joskwanten/msx-picoverse/2040/software/multirom/wireless/src/ESP8266_memio.asm

; ESP8266 TCP/IP UNAPI BIOS v.1.3
; Oduvaldo Pavan Junior
; ducasp@gmail.com
;    This code implements TCP/IP UNAPI Specification for MSX-SM
;
; Pieces of this code were based on DENYOTCP.ASM (Denyonet ROM)
; made by Konamiman
;
; This code also has contributions from KdL, most specifically in the Wi-Fi
; setup menus and functionality, he has helped quite a lot to get it to the
; final format and functionality, thanks!
;
; The MSX PICO version of this code has contribution from Jeroen Taverne That
; helped making some MACROs on the fixed / non speed optimized loop I/O parts
; of the code so we can easily switch this from I/O based to Memory Based.
;
; Note: this implementation depends upon ESP8266 having the UNAPI
; firmware flashed. This firmware has been developed by me as well.
;
; Usage is free as long as you publish your code changes. If you make a profit
; selling something using this code, a suggestion is that you donate one or two
; pieces of the hardware to the MSX DEV contest to be awarded to MSX DEV winners
; as this shouldn't cost much and perhaps will bring interest on developers to
; make games that support internet :)
;
; Design details:
; There are five instances of this ROM
;
; 1 - If configured as disabled in set-up menu item 4, or through setting F2
;     device to EF or keeping DEL pressed during boot, it won't load at all.
; 2 - F1 is pressed during boot, or through setting F2 device to F1, it will
;     show a setup menu, ESC resume boot.
; 3 - F2 is pressed during a soft reset, or trhough setting F2 device to F2 it
;     will force re-set of the ESP and re-connection to the AP.
; 4 - No key is pressed during a warm boot and F2 device is set to F0, UNAPI 
;     is enabled (default), EXTBIO HOOK for UNAPI calls is installed and HTIM_I
;     hook for internal usage and a few bytes at top of TPA are reserved upon
;     the first UNAPI function being called. No ESP reset or tries to set-up the
;     the RTC are done, so it is a quick warm-boot.
; 5 - No key is pressed during a cold boot or F2 is set to FE or any unknown
;     value, UNAPI is enabled (default), EXTBIO HOOK for UNAPI calls is installed
;     and HTIM_I hook for internal usage and a few bytes at top of TPA are reserved
;     upon the first UNAPI function being called. ESP is reset and if BIOS is set
;     up to do so, SNTP connection attempt is made and RTC is updated
;
; As a ROM, our segment is read only, so for RAM needs we need to use RAM not
; in our page. This ROM will do the following:
;
; If running the SETUP menu, we are going to "borrow" BASIC program area, that
; is saved at TXTTAB. We can't allocate memory at this point as any possible
; disk rom might be sitting on a slot that has not been initialized and results
; could be bad. The BASIC program area trick should be safe, unless some other
; cartridge runs a BASIC software for something (i.e.: wait disks be initialized
; ), in such case, that BASIC software or trick will most likely be corrupted
; after running our setup.
;
; After boot, we need RAM in the 4th page. We have the SLOT WORK AREA for free,
; it is 8 bytes reserved for our slot, and that is certainly not enough, just
; the EXTBIOS HOOK backup cost us 5 bytes, so we have three bytes remaining. Of
; those, we use two to indicate the bottom of the memory reserved in the 4th
; page. Whenever more memory is needed, HIMEM_RESERVED_SIZE must change, just
; remember that more memory reserved means less memory available to
; applications and BASIC, so use it wisely.
;
; Slot Work Area Details
; 0000 - 0004   : EXTBIO hook backup
; 0005 - 0006   : HIMEM Allocated area (starts with 00 xx, once allocated goes
;                 to Fxxx or Exxx so checking 0005 if 00 is enough)
; 007           : Unused
;
; Current HIMEM mapping offset related to the address stored in the 6th and 7th
; bytes of our slot work area:
;
; 0000 - 0004   : HTIM_I hook backup
; 0005 - 0006   : Counter that our HTIM_I hook updates
; 0007          : Store Single Byte some functions need
; 0008          : Stores whether DNS is ready or not
; 0009 - 000A   : Stores last DNS result
; 000B - 000C   : Stores a 16 bits value
; 000D - 0012   : Store a backup of BC / DE / HL
;   000D - 000E : C and B
;   000F - 0010 : D and E
;   0011 - 0012 : H and L
; 0013 - 001D   : Unused
;
; As this is sitting on a slot, there is a resoanable chance that this is initialized
; before any disk controllers. If that is the case, allocating memory at HIMEM is bad
; and might have two bad behaviors:
;
; 1 - Disk Controller is smart enough to determine HIMEM was moved and simply do not
; initialize. No disk available...
; 2 - Disk Controller doesn't care and simply wipe-out memory below original HIMEM at
; boot to create the disk interfaces static work area, thus, causing our allocated
; memory to be overwritten and MSX will most likely crash on ther first VDP interrupt
; after that...
;
; So, allocating memory at cartridge startup will make MSX freeze or misbehave or not
; have the disk available if our ROM is sitting in a slot lower than the disk. There
; are a few possibilities:
;
; 1 - Hook to H_STKE, it is called once all slots have been initialized... But, using
; this hook will make ESE SCSI to not work and halt with a "No enough memory" message,
; so I do not consider it a good option as the intention is to re-use code for other
; adapters.
; 2 - On any UNAPI call check the slot work area if the allocated area is other than 00
; and if it is, execute, otherwise, first execute our allocation routine. This has an
; overhead of a dozen instructions at every UNAPI function we execute, does not seem to
; impact performance compared to the UNAPI RAM driver that doesn't has it
; 3 - Try to go crazy and check for dos roms on slots above us, initialize those first
; if found... Too much trouble for a dozen instructions.
;
; So, for the moment the design decision is option #2
;
; F2 Device by KdL
; That device, present on recent OCM implementations, allow a byte to be saved and
; read from IO address F2. It has FF on start-up, and KdL devised the following
; values/states:
;
; FF - Default, meaning cold boot
; FE - Set this when an unexpected error occurred
; F2 - Equivalent to keeping F2 pressed at boot time, force the next warm boot
;      to try to detect the ESP8266
; F1 - Will force the Wi-Fi setup at next warm boot, so it is not needed to
;      keep F1 pressed
; F0 - Means that RTC has date and time, so the next warm boot doesn't check
;      for F1/F2 or try to update RTC, being faster
; EF - Set when ESP8266 was not found or by user at runtime to disable UNAPI
;      next warm boot
;
; MSX Pico also implements the F2 device

;*************************
;***  BUILD DEFINITIONS **
;*************************

;--- verbose rom...?
NON_VERBOSE_ROM:        equ 0
;--- Use memory mapped IO or not...
USE_MEM_IO:             equ 0

;*******************
;***  CONSTANTS  ***
;*******************

;--- System variables and routines:
CHGMOD:                 equ #005F
CHSNS:                  equ #009C
CHGET:                  equ #009F
CHPUT:                  equ #00A2
BEEP:                   equ #00C0
SNSMAT:                 equ #0141
KILBUF:                 equ #0156
LINLEN:                 equ #F3B0
CLIKSW:                 equ #F3DB
REG2SAV:                equ #F3E1
REG4SAV:                equ #F3E3
TXTTAB:                 equ #F676
ARG:                    equ #F847
HOKVLD:                 equ #FB20
HIMEM:                  equ #FC4A
CSRSW:                  equ #FCA9
EXPTBL:                 equ #FCC1
SLTWRK:                 equ #FD09
H_TIMI:                 equ #FD9F
H_CLEA:                 equ #FED0
EXTBIO:                 equ #FFCA


;--- Memory ports:
MEM_OUT_CMD_PORT:       equ #7F06
MEM_OUT_TX_PORT:        equ #7F07
MEM_IN_DATA_PORT:       equ #7F06
MEM_IN_STS_PORT:        equ #7F07
MEM_PORT_F2:            equ #7F05

;--- I/O ports:
OUT_CMD_PORT:           equ #06
OUT_TX_PORT:            equ #07
IN_DATA_PORT:           equ #06
IN_STS_PORT:            equ #07
PORT_F2:                equ #F2


    if USE_MEM_IO = 1
  MACRO SET_SPEED
    xor a
    ld  (MEM_OUT_CMD_PORT),a            ; Clear UART
  ENDM

  MACRO CLEAR_UART
    ld  a,20
    ld  (MEM_OUT_CMD_PORT),a            ; Clear UART
  ENDM

  MACRO SEND_DATA
    ld  (MEM_OUT_TX_PORT),a             ; Just send, no need to wait response
  ENDM

  MACRO RECEIVE_DATA
    ld a,(MEM_IN_DATA_PORT)
  ENDM

  MACRO LOAD_STS_PORT_IN_A
    ld  a,(MEM_IN_STS_PORT)
  ENDM

  MACRO CHECK_DATA
    ld  a,(MEM_IN_STS_PORT)
    bit 0,a                         ; If nz has data
  ENDM

  MACRO CHECK_QUICK_RECEIVE
    ld  a,(MEM_IN_STS_PORT)
    bit 3,a                         ; Quick Receive Supported?
  ENDM

  MACRO CHECK_BUFFER_UNDERRUN
    ld  a,(MEM_IN_STS_PORT)
    bit 4,a                         ; Buffer underrun?
  ENDM

  MACRO READ_F2
    ld  a,(MEM_PORT_F2)
  ENDM

  MACRO WRITE_F2
    ld  (MEM_PORT_F2),a
  ENDM
    else

  MACRO SET_SPEED
    xor a
    out (OUT_CMD_PORT),a            ; Clear UART
  ENDM

  MACRO CLEAR_UART
    ld  a,20
    out (OUT_CMD_PORT),a            ; Clear UART
  ENDM

  MACRO SEND_DATA
    out (OUT_TX_PORT),a             ; Just send, no need to wait response
  ENDM

  MACRO RECEIVE_DATA
    in a,(IN_DATA_PORT)
  ENDM

  MACRO LOAD_STS_PORT_IN_A
    in  a,(IN_STS_PORT)
  ENDM

  MACRO CHECK_DATA
    in  a,(IN_STS_PORT)
    bit 0,a                         ; If nz has data
  ENDM

  MACRO CHECK_QUICK_RECEIVE
    ld  a,(IN_STS_PORT)
    bit 3,a                         ; Quick Receive Supported?
  ENDM

  MACRO CHECK_BUFFER_UNDERRUN
    in  a,(IN_STS_PORT)
    bit 4,a                         ; Buffer underrun?
  ENDM

  MACRO READ_F2
    in  a,(PORT_F2)
  ENDM

  MACRO WRITE_F2
    out (PORT_F2),a
  ENDM
    endif

;--- API version and implementation version:
API_V_P:                equ 1
API_V_S:                equ 2
ROM_V_P:                equ 1
ROM_V_S:                equ 3

;--- Size of memory to reserve in upper TPA:
HIMEM_RESERVED_SIZE     equ 30

;--- Layout of our TPA area:
H_TIM_BACKUP_OFFSET     equ 0
MEMORY_COUNTER_OFFSET   equ 5
MEMORY_SB_VAR_OFFSET    equ 7
MEMORY_DNS_READY_OFFSET equ 8
MEMORY_DNS_RES_OFFSET   equ 9
MEMORY_DB_VAR_OFFSET    equ #0B
MEMORY_REGBACKUP_OFFSET equ #0D
MEMORY_BCBACKUP_OFFSET  equ #0D
MEMORY_DEBACKUP_OFFSET  equ #0F
MEMORY_HLBACKUP_OFFSET  equ #11

;--- Scan Page Size
SCAN_MAX_PAGE_SIZE      equ 8

;--- Maximum number of available standard and implementation-specific function
;--- numbers. Must be 0 to 127.
MAX_FN:                 equ 29

;--- Must be either zero (if no implementation-specific functions available),
;--- or 128 to 254.
MAX_IMPFN:              equ 0

;--- TCP/IP UNAPI error codes:
ERR_OK:                 equ 0
ERR_NOT_IMP:            equ 1
ERR_NO_NETWORK:         equ 2
ERR_NO_DATA:            equ 3
ERR_INV_PARAM:          equ 4
ERR_QUERY_EXISTS:       equ 5
ERR_INV_IP:             equ 6
ERR_NO_DNS:             equ 7
ERR_DNS:                equ 8
ERR_NO_FREE_CONN:       equ 9
ERR_CONN_EXISTS:        equ 10
ERR_NO_CONN:            equ 11
ERR_CONN_STATE:         equ 12
ERR_BUFFER:             equ 13
ERR_LARGE_DGRAM:        equ 14
ERR_INV_OPER:           equ 15

;--- TCP/IP UNAPI connection Status
UNAPI_TCPIP_NS_CLOSED   equ 0
UNAPI_TCPIP_NS_OPENING  equ 1
UNAPI_TCPIP_NS_OPEN     equ 2
UNAPI_TCPIP_NS_UNKNOWN  equ 255

;************************
;***  MSX ROM HEADER  ***
;************************
    org #4000
    db                  #41,#42
    dw                  INIT        ; Initialize ESP, if not found, won't install hook
    dw                  0           ; Statement
    dw                  0           ; Device
    dw                  0           ; Text
    ds                  6           ; Reserved

;==================
;===  Start-up  ===
;==================

INIT:
    ld  a,h                         ; Let's test if we are mirrored and being executed in wrong page
    cp  #40                         ; is MSB 0x40?
    ret nz                          ; if not, return, it is a mirror
    ; Let's set some System Variables
    xor a                           ; a = #00
    ld  (CSRSW),a                   ; cursor display is disabled
    ld  (CLIKSW),a                  ; when key press, key click disabled
    ; Let's intercept [DEL] key
    ld  a,8
    call    SNSMAT
    bit 3,a                         ; Test [DEL]
    ret z                           ; If DEL is pressed, UNAPI driver is not loaded and exits
    ; Let's check the Screen Mode, ref. https://www.msx.org/wiki/VDP_Table_Base_Address_Registers
    ld  a,(REG2SAV)
    cp  2
    jp  z,SCREEN_SETUP              ; If yes, is SCREEN 3
    ld  a,(REG4SAV)
    cp  0
    jr  z,IS_SCREEN1                ; If yes, is SCREEN 1
SCREEN_SETUP:
    ; Let's set the SCREEN 1
    ld  a,1                         ; a = #01
    rst #30
    db  0
    dw  CHGMOD                      ; SCREEN 1
IS_SCREEN1:
    ld  a,29                        ; WIDTH 29
    ld  (LINLEN),a
    ; We check if the Port F2 device is available
    READ_F2                         ; a = #FF, default value if it comes from power off or hard reset
    cpl                             ; a = #FF - a
    ld  c,a                         ; c = #00
    WRITE_F2                        ; a = #00
    ; Wait 250ms to ensure a successful hard reset even if you press the button very quickly
    call    WAIT_250MS_AND_THEN_CONTINUE
    READ_F2                         ; a = #00?
    cpl                             ; a = #FF - a
    WRITE_F2                        ; a = #FF?
    push    af
    ld  a,#FE                       ; Preset #FE, unexpected error
    WRITE_F2                        ; on port #F2
    pop af
    cp  c                           ; If not a = c, port #F2 is writable and available
    jr  z,BOOT_FROM_POWER_OFF       ; If a = c, port #F2 is not available, let's proceed as "boot from power off"
    ; Ok, Port F2 device available
    cp  #EF                         ; UNAPI driver has been disabled
    jr  nz,NOT_DISABLED_BY_F2       ; No, let's continue checking
    WRITE_F2                        ; If yes, UNAPI driver is not loaded and exits, but need to restore F2 port to not have a false error
    ret                             ; And our work is done
NOT_DISABLED_BY_F2:
    cp  #F0                         ; UNAPI driver has been loaded at least once
    jp  nz, F2_IS_NOT_F0            ; Ok, has not been loaded
    ; Let's intercept [F1] key
    ld  a,6
    call    SNSMAT
    bit 5,a                         ; Test [F1]
    jp  z,ENTERING_ESPSETUP         ; If F1 is pressed, let's execute our setup menu
    ; F1 is not pressed, continue
    bit 6,a                         ; Test [F2]
    jp  nz,INIT_UNAPI               ; If F2 is not pressed, let's proceed to INIT_UNAPI
    ; F2 is not pressed, continue
    jp  INIT_NOCLOCKUPDAT2          ; If yes, proceed without affecting the connection or the date and time
F2_IS_NOT_F0:
    cp  #F1                         ; User requested to go directly to Wi-Fi Setup
    jp  z,ENTERING_ESPSETUP         ; If yes, let's execute our setup menu
    cp  #F2                         ; User forces to check if ESP is installed
    jp  z,F2_IS_PRESSED             ; If yes, let's go check it out
    cp  #FE                         ; Unexpected error from the previous reboot
    jr  nz,BOOT_FROM_POWER_OFF      ; If no one is confirmed, let's proceed as "boot from power off"
    ; Oops! An unexpected error occurred on the last reboot
    ld  hl,STR_OOPS                 ; Print Oops! An unexpected error message
    call    PRINTHL                 ; and let's proceed as "boot from power off"
    ld  b,120                       ; Wait 2 seconds with message on screen
WAIT_2S:
    halt
    djnz    WAIT_2S                 ; If not zero, our time out has not elapsed
    ld  a,CLS
    call    CHPUT
BOOT_FROM_POWER_OFF:
    ; Let's intercept [F1] key
    ld  a,6
    call    SNSMAT
    bit 5,a                         ; Test [F1]
    jp  z,ENTERING_ESPSETUP         ; If F1 is pressed, let's execute our setup menu
    ; F1 is not pressed, continue
    if  NON_VERBOSE_ROM = 0
    ld  hl,WELCOME
    call    PRINTHL
    CHECK_QUICK_RECEIVE
    jr  nz,BOOT_FROM_POWER_OFF.1    ; QR Supported
    ld  hl,WELCOME_SF2
    call    PRINTHL
    jr  BOOT_FROM_POWER_OFF.2
BOOT_FROM_POWER_OFF.1:
    ld  hl,WELCOME_SF
    call    PRINTHL
BOOT_FROM_POWER_OFF.2:
    endif
    ld  a,6
    call    SNSMAT
    bit 6,a                         ; Test [F2]
    jp  nz,INIT_UNAPI               ; If F2 is not pressed, let's proceed to INIT_UNAPI
    ; F2 is pressed, continue
F2_IS_PRESSED:
    call    RESET_ESP
    or  a
    jr  nz,ESP_NOT_FOUND
    ld  hl,OK_S                     ; Properly detected
    jp  INIT_F_MSG                  ; Well, if reset successful, continue
ESP_NOT_FOUND:
    ; If here, ESP was not found, so, exit with an error message
    ld  a,b
    or  a
    ld  hl,FAIL_S                   ; If 0, non responsive
    jr  z,INIT_F_MSG
    ld  hl,FAIL_F                   ; Otherwise, firmware is old
INIT_F_MSG:
    call    PRINTHL
INIT_F_WAIT:
    ld  b,180                       ; 3s
INIT_F_LOOP_WAIT:
    halt
    djnz    INIT_F_LOOP_WAIT
AND_DONE:
    ld  a,#EF                       ; Set #EF, ESP Not Found
    WRITE_F2                        ; on port #F2
    ret                             ; And done
INIT_UNAPI:
    CLEAR_UART
    ld  a,CMD_QUERY_ACLK_SETTINGS
    SEND_DATA
    ld  hl,60                       ; Wait Up To 1s
    ld  de,(TXTTAB)                 ; We will borrow Basic Program memory area for now...
    ld  ixl,e
    ld  ixh,d                       ; Address in IX
    call    WAIT_MENU_CMD_RESPONSE
    jp  z,INIT_NOCLOCKUPDATE        ; If error, just skip
    ; Response received, IX+0 and IX+1 has Auto Clock and GMT
    ld  a,3
    cp  (ix+0)
    jr  nz,INIT_UNAPI2              ; If not disabled continue on INIT_UNAPI2
    ; Disabled, ok, so let's ensure connection is not locked (just in case it was setup as disabled right now)
    CLEAR_UART
    ld  a,CMD_WIFIRELEASE_ESP
    SEND_DATA                       ; Just send, no need to wait response
    ret
INIT_UNAPI2:
    ld  a,(#002D)                   ; Check MSX Version
    or  a
    jr  z,INIT_NOCLOCKUPDATE        ; If zero, MSX1, can't set clock
    xor a
    or  (ix+0)
    jr  z,INIT_NOCLOCKUPDATE        ; if turned off, skip
    ; Ok, not zero, so we are going to simply request the time, it might take up to 10s
    inc ix
    inc ix                          ; ok, leave IX+0 and IX+1 intact
    ; b = number of response check attempts
    ld  b,5                         ; 5 * 2s = 10s
    CLEAR_UART
    ld  a,CMD_GET_TIME
    SEND_DATA
TRY_AGAIN:
    push    bc
    ld  hl,120                      ; Wait Up To 2s per attempt
    call    WAIT_MENU_CMD_RESPONSE
    jr  nz,INIT_CLOCKUPDATE         ; if ok, follow up
    ld  hl,STR_WAITING              ; Print Waiting for connection message
    call    PRINTHL
    ld  a,#ff
    cp  b                           ; Was time-out the failure reason?
    pop bc                          ; Restore stack ballance and retry counter
    jr  nz,STOP_TRYING              ; If error return code and not time-out, no more checks needed
    ld  a,CMD_GET_TIME              ; Needed for retries
    djnz    TRY_AGAIN
STOP_TRYING:
    ; Leave a message that clock has not been updated
    ld  hl,STR_CLKUPDT_FAIL
    call    PRINTHL
    ld  a,240                       ; Wait 4 seconds with message on screen
WAIT_4S:
    halt
    dec a
    ; If not zero, our time out has not elapsed
    jr  nz,WAIT_4S
    jr  INIT_NOCLOCKUPDATE          ; error, just skip to not set garbage in clock
INIT_CLOCKUPDATE:
    pop bc
    dec ix
    dec ix                          ; ix back where it should
    ; ix + 0 -> 0 If no need to set clock, 1 if set clock, 2 if set clock and request to turn Wi-Fi Off
    ; ix + 1 -> GMT setting, well, not going to use it
    ; ix + 2 -> Seconds
    ; ix + 3 -> Minutes
    ; ix + 4 -> Hours
    ; ix + 5 -> Day
    ; ix + 6 -> Month
    ; ix + 7 -> Year LSB
    ; ix + 8 -> Year MSB
    ld  h,(ix+4)
    ld  l,(ix+3)
    ld  d,(ix+2)
    call    SET_TIME
    jr  nz,INIT_NOCLOCKUPDATE       ; if error, just skip
    ld  h,(ix+8)
    ld  l,(ix+7)
    ld  d,(ix+6)
    ld  e,(ix+5)
    call    SET_DATE
    ld  a,2
    cp  (ix+0)
    jr  nz,INIT_NOCLOCKUPDATE
    ; First, release any hold to Wi-Fi Connection
    CLEAR_UART
    ld  a,CMD_WIFIRELEASE_ESP
    SEND_DATA                       ; Just send, no need to wait response
    ; And, turn off Wi-Fi Immediatelly
    CLEAR_UART
    ld  a,CMD_WIFI_OFF
    SEND_DATA                       ; Just send, no need to wait response
    jr  INIT_NOCLOCKUPDAT2
INIT_NOCLOCKUPDATE:
    ; Release any hold to Wi-Fi Connection
    CLEAR_UART
    ld  a,CMD_WIFIRELEASE_ESP
    SEND_DATA                       ; Just send, no need to wait response
INIT_NOCLOCKUPDAT2:
    ; Save existing EXTBIO hook if it exists
    ld  a,(HOKVLD)
    bit 0,a
    jr  nz,SAVE_HOOK2               ; HOKVLD tells us if there is an extended BIOS already or not, if yes, save it
    ; If here, no extended BIOS
    call    GETSLT
    call    GETWRK                  ; Our ROM work area address is at HL (we can use up to 8 bytes)
    ld  a,#c9                       ; RET, as we are the first extended BIOS
    ld  (hl),a
    jr  PATCH                       ; And now all we need to do is patch the EXTBIO hook :)

SAVE_HOOK2:
    ; If here, we are not the first to extend bios, so we need to save the previous one
    call    GETSLT
    call    GETWRK                  ; Our ROM work area address is at HL (we can use up to 8 bytes)
    ex  de,hl                       ; It is the destination for....
    ld  hl,EXTBIO                   ; The actual EXTBIO hook
    ld  bc,5                        ; That is 5 bytes large
    ldir                            ; And move to our work area
    xor a
    ld  (de),a                      ; Not initialized (de is at the sixth byte) of our slot work area
    inc de
    ld  (de),a                      ; Not initialized (de is at the seventh byte) of our slot work area

    ; Patch EXTBIO
PATCH:
    ld  a,#F7                       ; RST #30
    ld  (EXTBIO),a                  ; In EXTBIO hook
    call    GETSLT                  ; Our Slot in A
    ld  (EXTBIO+1),a                ; Next EXTBIO hook byte
    ld  hl,DO_EXTBIO                ; Our EXTBIO routine address
    ld  (EXTBIO+2),hl               ; Goes to the following two bytes in the hook

    ld  hl,EXTBIO+5                 ; Must patch DISINT and ENAINT as well
    ld  b,5*2
PATCH2:
    ld  (hl),#C9
    inc hl
    djnz    PATCH2                  ; So patch all 10 bytes with return

    ld  hl,HOKVLD
    set 0,(hl)                      ; And set HOKVLD properly to indicate an EXTBIOS is installed
INIT_OK:
    if  NON_VERBOSE_ROM = 0
    ld  hl,OK_S                     ; All done and set, nice exit message
    call    PRINTHL
    endif
    ld  a,#F0                       ; Set #F0, UNAPI driver has been loaded at least once
    WRITE_F2
    ret

;==============================
;===  TPA Memory Allocation  ==
;==============================
HIMEM_ALLOC:
    ; Now let's reserve memory in the 4th page for our usage
    ld hl,(HIMEM)                   ; Get HIMEM
    or  a                           ; Clear Carry
    ld  de,HIMEM_RESERVED_SIZE      ; Reserve How much memory we need
    sbc hl,de                       ; New HIMEM
    ld  (HIMEM),hl                  ; Save it
    inc hl                          ; To be safe
    ex  de,hl                       ; now in DE
    call    GETSLT
    call    GETMEMPOINTERADDR       ; This is where we are going to store our memory area address
    ; GETSLT and GETMEMPOINTER do not change DE, so it still has the our memory area address
    ld  (hl),e
    inc hl
    ld  (hl),d                      ; And save our memory area there
    ; Ok, DE has our memory area, let's save old H_TIMI hook there
    ld  hl,H_TIMI                   ; The actual H_TIMI hook
    ld  bc,5                        ; That is 5 bytes large
    ldir                            ; And move to our memory area
    di                              ; Turn of interrupts as we are going to patch H_TIMI
PATCH_H_TIMI:
    ld  a,#F7                       ; RST #30
    ld  (H_TIMI),a                  ; In H_TIMI hook
    call    GETSLT                  ; Our Slot in A
    ld  (H_TIMI+1),a                ; Next H_TIMI hook byte
    ld  hl,DO_HTIMI                 ; Our H_TIMI routine address
    ld  (H_TIMI+2),hl               ; Goes to the following two bytes in the hook
    ei                              ; done, so re-enable interrupts

    ; Set DNS_READY to zero
    xor a
    call    SETDNSREADY
    ; Set TIME-OUT counter to zero
    ld  hl,0
    call    SETCOUNTER
    ret

;============================
;===  SETUP Menu Routines  ==
;===       Main Menu       ==
;============================
ESPSETUP.EXIT:
    ld  a,CLS
    call    CHPUT
    jp  INIT_UNAPI                  ; When done, resume initialization
ENTERING_ESPSETUP:
    ld  hl,ENTERING_WIFI_SETUP
    call    PRINTHL
    call    PATTERN_SETUP
    call    WAIT_250MS_AND_THEN_CONTINUE
    ; Hold Wi-Fi Connection On
    CLEAR_UART
    ld  a,CMD_WIFIHOLD_ESP
    SEND_DATA
    ld  hl,60                       ; Up to 1s time-out
    call    WAIT_MENU_CMD_RESPONSE  ; Wait response
    ; We do not want to error here, just in case user still need to upgrade ESP firmware
ESPSETUP:
    call    RESET_ESP
    or  a
    jp  nz,ESP_NOT_FOUND            ; Not well, ESP was not found
    ; Well, if reset successful, continue
    ld  hl,WELCOME
    call    PRINTHL
    CHECK_QUICK_RECEIVE
    jr  nz,ESPSETUP.2NF             ; If yes, tells Quick Receive support
    ld  hl,WELCOME_SF2
    call    PRINTHL                 ; Print Welcome message no QR
    jr  ESPSETUP.3NF
ESPSETUP.2NF:
    ld  hl,WELCOME_SF
    call    PRINTHL                 ; Print Welcome message QR
ESPSETUP.3NF:
    ld  hl,WELCOME_CS
    call    PRINTHL                 ; Print Wi-Fi is reconnecting to:
ESPSETUP_NEXT:
    call    KILBUF                  ; Clear Keyboard Buffer
    ld  hl,WELCOME_NEXT
    call    PRINTHL
    ld  hl,WELCOME_SF_NEXT
    call    PRINTHL                 ; Print Empty Welcome message
    call    GET_AP_STAT
    jp  z,ESPSETUP_NEXT.1G          ; Won't block in case of error
    ; Success, so connection state is in IX+0, then, zero terminated string with SSID starting at IX+1
    ld  a,(ix+0)
    ld  hl,WELCOME_CS0_NEXT
    cp  0
    jr  z,ESPSETUP_NEXT.2F
    ld  hl,WELCOME_CS1_NEXT
    cp  1
    jr  z,ESPSETUP_NEXT.2F
    ld  hl,WELCOME_CS2_NEXT
    cp  2
    jr  z,ESPSETUP_NEXT.2F
    ld  hl,WELCOME_CS3_NEXT
    cp  3
    jr  z,ESPSETUP_NEXT.2F
    ld  hl,WELCOME_CS4_NEXT
    cp  4
    jr  z,ESPSETUP_NEXT.2F
    ld  hl,WELCOME_CS5_NEXT
ESPSETUP_NEXT.2F:
    ld  iyh,a                       ; Save current conn status in iyh
    call    PRINTHL                 ; Print Status
    push    ix
    pop hl
    inc hl                          ; HL has AP Name
    call    PRINTHLINE              ; Print AP Name
ESPSETUP_NEXT.1G:
    ld  hl,MMENU_S_NEXT
    call    PRINTHL                 ; Print Main Menu
MM_CURSOR_BLINK:
    call    MM_CURSOR_SW            ; Cursor On
CONN_CHG_LOOP:
    call    CHSNS
    jr  nz,MM_WAIT_INPUT            ; If not zero, there is a key in buffer
    ; Ok, there is not, we can check if connection status changed
    call    GET_AP_STAT
    jp  z,CONN_CHG_LOOP             ; Won't block in case of error
    ; Success, so connection state is in IX+0
    ld  a,(ix+0)
    cp  iyh                         ; If same, zero
    jr  z,CONN_CHG_LOOP             ; Keep loop
    call    MM_CURSOR_SW            ; Cursor Off
    jp  ESPSETUP_NEXT               ; Changed, re-build menu
MM_WAIT_INPUT:
    call    CHGET
    cp  #1b                         ; ESC?
    jp  z,ESPSETUP.EXIT             ; When done, resume initialization
    cp  '1'                         ; Setup Nagle?
    jp  z,SET_NAGLE
    cp  '2'                         ; Setup Wi-Fi On Period?
    jp  z,SET_WIFI_TIMEOUT
    cp  '3'                         ; Scan networks?
    jp  z,START_WIFI_SCAN
    cp  '4'                         ; Automatic Setting of Clock?
    jp  z,START_CLK_AUTO
    call    BEEP                    ; Wrong Input, beep
    call    MM_CURSOR_SW            ; Cursor Off
    halt
    jp  MM_CURSOR_BLINK             ; And return, waiting another key
MM_CURSOR_SW:                       ; Cursor workaround for CONN_CHG_LOOP
    ld  a,GOLEFT
    call    CHPUT
    ld  a,1
    ld  (CSRSW),a
    ld  a,' '
    call    CHPUT                   ; Switch the cursor display mode
    xor a
    ld  (CSRSW),a
    ret
GET_AP_STAT:                        ; Use 'call GET_AP_STAT'
    CLEAR_UART
    ld  a,CMD_AP_STS
    SEND_DATA                       ; Get AP conn status and name
    ld  hl,60                       ; Wait Up To 1s
    ld  de,(TXTTAB)                 ; We will borrow Basic Program memory area for now...
    ld  ixl,e
    ld  ixh,d                       ; Address in IX
    jp  WAIT_MENU_CMD_RESPONSE

;============================
;===  SETUP Menu Routines  ==
;===  Wi-Fi and Clock Menu ==
;============================
CLK_MSX1_GO:
    ld  hl,MMENU_CLOCK_MSX1
    call    PRINTHL                 ; Print Main Clock MSX1 message
    call    ISCLKAUTO
    ld  a,(ix+0)                    ; Auto Clock Current setting
    cp  3                           ; If 3 adapter disabled
    jr  z,CLK_MSX1_ADAPTERDIS
    ld  hl,MMENU_CLOCK_0
    call    PRINTHL
    jr  CLK_MSX1_OPT
CLK_MSX1_ADAPTERDIS:
    ld  hl,MMENU_CLOCK_3
    call    PRINTHL
CLK_MSX1_OPT:
    ld  hl,MMENU_CLOCK_OPT
    call    PRINTHL
CLK_MSX1_WAIT_OPT_INPUT:
    call    CHGET
    cp  #1b                         ; ESC?
    jp  z,ESPSETUP                  ; Back to main menu
    cp  '0'
    jp  z,CLK_MSX1_SEND_CMD
    cp  '3'
    jp  z,CLK_AUTO_WAIT_GMT
    call    BEEP                    ; Wrong Input, beep
    jp  CLK_MSX1_WAIT_OPT_INPUT     ; And return, waiting another key
CLK_MSX1_SEND_CMD:
    call    CHPUT                   ; Print option
    sub '0'                         ; Adjust format
    ld  (ix+0),a                    ; Save it
    ld  a,#0d
    call    CHPUT
    ld  a,#0a
    call    CHPUT
    jp  CLK_AUTO_GMT_CHK_DONE       ; And sending the command will be done there

START_CLK_AUTO:
    ld  a,'4'
    call    CHPUT
    call    WAIT_250MS_AND_THEN_CONTINUE
    ld  a,(#002D)                   ; Check MSX Version
    or  a
    jp  z,CLK_MSX1_GO               ; If zero, MSX1, so can just enable or disable adapter
CLK_AUTO_GO:
    ld  hl,MMENU_CLOCK_MSX2
    call    PRINTHL                 ; Print Main Clock MSX2 message
    call    ISCLKAUTO
    ld  a,(ix+0)                    ; Auto Clock Current setting
    or  a                           ; If zero, off
    jr  nz,CLK_AUTO_CHK1
    ld  hl,MMENU_CLOCK_0
    call    PRINTHL
    jr  CLK_AUTO_GMT_OPT
CLK_AUTO_CHK1:
    dec a                           ; If 1, on and keep wifi on
    jr  nz,CLK_AUTO_CHK2
    ld  hl,MMENU_CLOCK_1
    call    PRINTHL
    jr  CLK_AUTO_GMT
CLK_AUTO_CHK2:
    dec a                           ; If 2, on and turn wifi off
    jr  nz,CLK_AUTO_3
    ld  hl,MMENU_CLOCK_2
    call    PRINTHL
    jr  CLK_AUTO_GMT
CLK_AUTO_3:
    ld  hl,MMENU_CLOCK_3
    call    PRINTHL
    jr  CLK_AUTO_GMT_OPT
CLK_AUTO_GMT:
    ld  h,(ix+1)                    ; Save it for now
    ld  a,(ix+1)                    ; GMT current setting
    bit 7,a                         ; If set, is -
    jr  z,CLK_AUTO_GMTP
    ld  a,'-'
    call    CHPUT
    res 7,(ix+1)                    ; Clear - indicator
    jr  CLK_AUTO_GMTM
CLK_AUTO_GMTP:
    ld  a,'+'
    call    CHPUT
CLK_AUTO_GMTM:
    ld  a,9
    cp  (ix+1)                      ; Greater than 9?
    jr  nc,CLK_AUTO_GMTD            ; If not, just print what is in A + '0'
    ld  a,'1'                       ; It is 1
    call    CHPUT
    ld  a,(ix+1)
    add '0'-10                      ; Need to subtract 10 and add '0' to print
    call    CHPUT
    jr  CLK_AUTO_GMT_OPT
CLK_AUTO_GMTD:
    ld  a,'0'
    add a,(ix+1)                    ; Our value
    call    CHPUT
    ld  (ix+1),h                    ; Restore original value
CLK_AUTO_GMT_OPT:
    ld  hl,MMENU_CLOCK_OPT
    call    PRINTHL
CLK_AUTO_WAIT_OPT_INPUT:
    call    CHGET
    cp  #1b                         ; ESC?
    jp  z,ESPSETUP                  ; Back to main menu
    cp  '0'
    jp  z,CLK_AUTO_WAIT_GMT
    cp  '1'
    jp  z,CLK_AUTO_WAIT_GMT
    cp  '2'
    jp  z,CLK_AUTO_WAIT_GMT
    cp  '3'
    jp  z,CLK_AUTO_WAIT_GMT
    call    BEEP                    ; Wrong Input, beep
    jp  CLK_AUTO_WAIT_OPT_INPUT     ; And return, waiting another key
CLK_AUTO_WAIT_GMT:
    call    CHPUT                   ; Print option
    sub '0'                         ; Adjust format
    ld  (ix+0),a                    ; Save it
    or  a
    jp  z,CLK_AUTO_GMT_CHK_DONE     ; And send the command if just disabling clock auto set
    cp  3
    jp  z,CLK_AUTO_GMT_CHK_DONE     ; Or send the command if just disabling the adapter
    ld  hl,MMENU_GMT_OPT
    call    PRINTHL
    ld  d,0                         ; # of digits entered
    ld  e,0                         ; # of characters printed
    ld  (ix+1),0                    ; GMT 0
CLK_AUTO_WAIT_GMT_INPUT:
    call    CHGET
    cp  #1b                         ; ESC?
    jp  z,ESPSETUP                  ; Back to main menu
    cp  #0d                         ; ENTER?
    jp  z,CLK_AUTO_GMT_CHK_INPUT    ; Check if ok to send command
    cp  #08                         ; Backspace?
    jp  z,CLK_AUTO_GMT_CHK_BS       ; Check if there is something to erase
    cp  '-'                         ; Negative value?
    jp  z,CLK_AUTO_GMT_CHK_INPUT
    cp  '0'                         ; >=0?
    jp  c,CLK_AUTO_GMT_BAD_INPUT    ; If not, bad input
    cp  '9'+1                       ; <= 9
    jp  nc,CLK_AUTO_GMT_BAD_INPUT   ; If not, bad input
    jp  CLK_AUTO_GMT_CHK_INPUT      ; Otherwise, validate digit
CLK_AUTO_GMT_CHK_BS:
    xor a
    cp  e                           ; Anything on screen?
    jr  z,CLK_AUTO_GMT_BAD_INPUT    ; Nothing to erase
    dec e                           ; One less character on the screen
    cp  d                           ; Any digit?
    jr  z,CLK_AUTO_GMT_CHK_BS_MIN   ; If not, just erase - sign
    ; There is, so it is one less digit
    dec d
    jr  CLK_AUTO_GMT_CHK_DIGIT
CLK_AUTO_GMT_CHK_BS_MIN:
    ld  (ix+1),0                    ; Reset sign
CLK_AUTO_GMT_CHK_DIGIT:
    ld  a,8                         ; Backspace
    call    CHPUT                   ; Print it
    ld  a,' '                       ; Space
    call    CHPUT                   ; Print it
    ld  a,8                         ; Backspace
    call    CHPUT                   ; Print it
    jp  CLK_AUTO_WAIT_GMT_INPUT     ; Return
CLK_AUTO_GMT_BAD_INPUT:
    ; Beep might use sub rom, and if so, all registers will be messed up, better save
    push    bc
    push    de
    push    af
    push    hl
    call    BEEP                    ; Wrong Input, beep
    pop hl
    pop af
    pop de
    pop bc
    jp  CLK_AUTO_WAIT_GMT_INPUT     ; And return, waiting another key
CLK_AUTO_GMT_CHK_INPUT:
    ld  c,a                         ; Save in C for printing if needed
    cp  '-'                         ; - sign?
    jr  nz,CLK_AUTO_GMT_CHK_CR      ; If not, check if enter
    ; - sign
    ld  a,0
    cp  e                           ; If not the first character, can't accept
    jr  nz,CLK_AUTO_GMT_BAD_INPUT
    ; It is the first, so let's print it
    ld  a,c
    call    CHPUT
    ld  (ix+1),0x80                 ; Set the - sign bit, for now rest is zero
    inc e                           ; Increase # of characters printed
    jp  CLK_AUTO_WAIT_GMT_INPUT     ; Continue waiting input
CLK_AUTO_GMT_CHK_CR:
    cp  #0d                         ; ENTER?
    jr  nz,CLK_AUTO_GMT_CHK_CD      ; If not, check if digit is valid
    ; Enter
    ld  a,0
    cp  d                           ; Ok, at least one digit entered?
    jr  z,CLK_AUTO_GMT_BAD_INPUT    ; No, so, enter is no good now
    ; It is, if it had a digit entered and did not send, it was 1, so...
    ld  a,1
    or  a,(ix+1)                    ; Adjust sign, if needed
    ld  (ix+1),a                    ; Save
    jr  CLK_AUTO_GMT_CHK_DONE       ; Ok, ready to send
CLK_AUTO_GMT_CHK_CD:
    ; Ok, it is a digit
    ld  b,'0'
    sub a,b                         ; A has digit value
    ld  b,a                         ; Save in B
    ld  a,0
    cp  d
    jr  nz,CLK_AUTO_GMT_CHK_CSD     ; If not zero, it is second digit, so almost done
    ; 1st digit, let's check if it is other than 1, if it is, we are almost done
    ld  a,1
    cp  b
    jr  z,CLK_AUTO_GMT_CHK_CD.1     ; If it is 1, wait next digit or enter
    ; Not 1, so just adjust ix+1 and go
    ld  a,c
    call    CHPUT                   ; Print it
    ld  a,b
    or  a
    jr  z,CLK_AUTO_SKIP_SIGN
    or  a,(ix+1)                    ; Adjust sign, if needed
CLK_AUTO_SKIP_SIGN:
    ld  (ix+1),a                    ; Save
    jr  CLK_AUTO_GMT_CHK_DONE       ; Ok, ready to send
CLK_AUTO_GMT_CHK_CD.1:
    ld  a,c
    call    CHPUT                   ; Print it
    inc d                           ; Digits entered now is 1
    inc e                           ; Digits printed increased
    jp  CLK_AUTO_WAIT_GMT_INPUT     ; Continue waiting input
CLK_AUTO_GMT_CHK_CSD:
    ; Second digit, easy... First was 1, now need to check if it is 0, 1 or 2, otherwise, bad entry
    ld  a,b
    ld  b,3
    cp  b
    jp  nc,CLK_AUTO_GMT_BAD_INPUT   ; 3 or more, so, not valid
    or  a                           ; Is it zero?
    jr  nz,CLK_AUTO_GMT_CHK_CSD1    ; If not, check for 1
    ; It was zero
    ld  a,10                        ; So, 10
    or  a,(ix+1)                    ; Adjust sign, if needed
    ld  (ix+1),a                    ; Save
    ld  a,c
    call    CHPUT                   ; Print it
    jr  CLK_AUTO_GMT_CHK_DONE       ; Ready to
CLK_AUTO_GMT_CHK_CSD1:
    dec a                           ; Is it one?
    jr  nz,CLK_AUTO_GMT_CHK_CSD2
    ; It was one
    ld  a,11                        ; So, eleven
    or  a,(ix+1)                    ; Adjust sign, if needed
    ld  (ix+1),a                    ; Save
    ld  a,c
    call    CHPUT                   ; Print it
    jr  CLK_AUTO_GMT_CHK_DONE       ; Ready to send
CLK_AUTO_GMT_CHK_CSD2:
    ; It was two
    ld  a,12                        ; So, twelve
    or  a,(ix+1)                    ; Adjust sign, if needed
    ld  (ix+1),a                    ; Save
    ld  a,c
    call    CHPUT                   ; Print it
    ; And send command
CLK_AUTO_GMT_CHK_DONE:
    ld  a,#0d
    call    CHPUT
    ld  a,#0a
    call    CHPUT
    ld  hl,STR_SENDING
    call    PRINTHL
    CLEAR_UART
    ld  a,CMD_SET_ACLK_SETTINGS
    SEND_DATA
    ld  a,0                         ; Size MSB is 0
    SEND_DATA
    ld  a,2                         ; Size LSB is 2
    SEND_DATA
    ld  a,(ix+0)                    ; Option
    SEND_DATA
    ld  a,(ix+1)                    ; GMT
    SEND_DATA
    ld  hl,60                       ; Wait Up To 1s
    ld  a,CMD_SET_ACLK_SETTINGS
    call    WAIT_MENU_QCMD_RESPONSE
    ld  hl,STR_SENDING_OK
    jr  nz,CLK_AUTO_GMT_CHK_RESULT
    ld  hl,STR_SENDING_FAIL
CLK_AUTO_GMT_CHK_RESULT:
    call    PRINTHL
    jp  WAIT_2S_AND_THEN_MAINMENU

;============================
;===  SETUP Menu Routines  ==
;===    Wi-Fi Scan Menu    ==
;============================
START_WIFI_SCAN:
    ld  a,'3'
    call    CHPUT
    call    WAIT_250MS_AND_THEN_CONTINUE
START_WIFI_RESCAN:
    ld  hl,MMENU_SCAN
    call    PRINTHL                 ; Print Main Scan message
    call    STARTWIFISCAN           ; Request Wi-Fi Scan to start
    ld  de,(TXTTAB)                 ; We will borrow Basic Program memory area for now...
    ld  ixl,e
    ld  ixh,d                       ; Address in IX
    ld  de,20                       ; At least 10s waiting scan to finish, retry 20 times waiting 0.5s between attempts
WIFI_SCAN_WAIT_END:
    CLEAR_UART
    ld  a,CMD_SCAN_RESULTS
    SEND_DATA
    ld  hl,60                       ; Wait Up To 1s
    call    WAIT_MENU_SCMD_RESPONSE
    jp  nz,WIFI_SCAN_SHOW_LIST      ; if success show the list
    ld  a,b
    cp  2                           ; If 2, scan is done and nothing found
    jp  z,WIFI_SCAN_NONETWORKS
    ld  l,30
WIFI_SCAN_WAITHS:
    halt
    dec l
    jr  nz,WIFI_SCAN_WAITHS
    dec de
    ld  a,e
    or  d
    jp  z,WIFI_SCAN_TIMEOUT
    jp  WIFI_SCAN_WAIT_END
WIFI_SCAN_SHOW_LIST:
    ld  d,a                         ; Save access point counter here
    ld  e,0                         ; And here how many were printed
    ld  hl,MMENU_SCANS
    call    PRINTHL
    push    ix
    pop hl                          ; IX in HL
WIFI_LIST_LOOP:
    ld  a,e
    add a,'0'                       ; Convert to number
    call    CHPUT
    ld  a,' '                       ; Space
    call    CHPUT
    ld  a,'-'                       ; Dash
    call    CHPUT
    ld  a,' '                       ; Space
    call    CHPUT
    ld  b,24                        ; Cuts AP names > 23 chars
PRT_APNAMELP:
    ld  a,(hl)
    or  a
    jp  z,PRT_APENC
    call    CHPUT
    inc hl
    djnz    PRT_APNAMELP
    push    hl
    ld  hl,SCAN_TERMINATOR_CUT
    call    PRINTHL
    pop hl
PRT_APNAMELP_CUT:
    ld  a,(hl)
    or  a
    jp  z,PRT_APENC
    inc hl
    jp  PRT_APNAMELP_CUT
PRT_APENC:
    inc hl
    ld  a,(hl)
    or  a
    jp  z,PRT_APNOTENC
    push    hl
    ld  hl,SCAN_TERMINATOR_ENC
    call    PRINTHL
    pop hl
    jp  PRT_AP_CHKLOOP
PRT_APNOTENC:
    push    hl
    ld  hl,SCAN_TERMINATOR_OPEN
    call    PRINTHL
    pop hl
PRT_AP_CHKLOOP:
    inc hl
    inc e
    ld  a,SCAN_MAX_PAGE_SIZE
    cp  e
    jp  z,APLIST_OVERFLOW
    dec d
    jp  nz,WIFI_LIST_LOOP
    ld  b,0                         ; Signal no more list data
    jr  APLIST_NO_OVERFLOW
APLIST_OVERFLOW:
    dec d                           ; Update remaining items
    xor a
    or  d                           ; Still has items?
    jr  z,APLIST_NO_OVERFLOW        ; No more items
    ld  b,1                         ; Signal that there still is data pending to list in another page
    push    hl
    pop iy                          ; Save in IY the address to continue from
    ld  c,d                         ; And C has the remaining AP count
    ld  hl,MMENU_SCANQM
    jr  APLIST_NOFLW
APLIST_NO_OVERFLOW:
    ; If here, current page has been printed
    ; E has the maximum allowable AP number
    ; B will indicate if there are more items for a next page
    ; IY will hold the address of the following items
    ; Let's ask which one to connect
    ld  hl,MMENU_SCANQ
APLIST_NOFLW:
    call    PRINTHL                 ; Show message asking which network to connect
    ld  a,'0'
    add a,e
    ld  e,a                         ; To make it easy in the selection screen
WIFI_SELECT_AP:
    call    CHGET
    cp  #1b                         ; ESC?
    jp  z,ESPSETUP                  ; When done, back to main setup
    cp  #20                         ; Spacebar?
    jp  z,WIFI_SELECT_SPACEBAR      ; Check if re-scan or next page
    cp  CR                          ; ENTER?
    jp  z,WIFI_CONNECT_ME_CHOOSEN   ; Request AP Name and Password if needed
    cp  '0'                         ; Check if A is less than 0
    jp  c,INPUT_WFSAP_BAD_INPUT     ; If it is, ignore
    cp  e                           ; Check if a is greater than what is in E
    jp  nc,INPUT_WFSAP_BAD_INPUT    ; If it is, ignore
    jp  WIFI_CONNECT_SELECTION_OK   ; Selection Ok if here

WIFI_SELECT_SPACEBAR:
    xor a
    or  d                           ; D = AP counter
    jp  z,START_WIFI_RESCAN         ; Rescan if no more items
    ; Otherwise, more items, start at IY
    push    iy
    pop ix                          ; Restore the list from where we finished last time
    ld  a,c                         ; Restore the remaining APs to list
    jp  WIFI_SCAN_SHOW_LIST         ; And show

WIFI_CONNECT_ME_CHOOSEN:
    ld  hl,MMENU_MANUALENTRY
    call    PRINTHL                 ; Show message asking AP details....
    ; IX has the AP list, we don't care, but that address is ours to use to handle SSID Entry
    push    ix
    pop hl                          ; HL has the address
    ld  c,0                         ; AP name size
WIFI_CONNECT_MANUAL_ENTRY:
    call    CHGET
    cp  #1b                         ; ESC?
    jp  z,ESPSETUP                  ; Back to main setup
    cp  #08                         ; Backspace?
    jr  z,WIFI_CONNECT_ME_BS        ; Check if there is something to erase
    cp  #0d                         ; ENTER?
    jr  z,WIFI_ME_CHECK_INPUT       ; Check if ok
    ; Otherwise it is a digit
    ld  (hl),a
    ld  a,c
    sub 32                          ; SSID maximum is 32 characters
    jr  z,WIFI_CONNECT_MANUAL_ENTRY
    ld  a,(hl)
    inc c
    inc hl
    cp  32
    jr  nc,WIFI_CONNECT_ME_CHKPRT2  ; Ok, not below space, but is it delete?
    ld  a,'?'                       ; Prints a question mark
    jr  WIFI_CONNECT_ME_CHKPRTD
WIFI_CONNECT_ME_CHKPRT2:
    cp  #7f
    jr  nz,WIFI_CONNECT_ME_CHKPRTD
    ld  a,'?'                       ; Prints a question mark if it is delete
WIFI_CONNECT_ME_CHKPRTD:
    call    CHPUT                   ; Print a char
    jp  WIFI_CONNECT_MANUAL_ENTRY
WIFI_CONNECT_ME_0_TERM:
    xor a
    ld  (hl),a
    inc hl
    push    hl                      ; Save it
    ld  hl,MENU_MANUALENTRY_PWD
    call    PRINTHL                 ; We are asking if password is needed
    pop hl                          ; Restore it
    call    CHGET                   ; Get key, if Y or y, needed, otherwise not
    res 5,a                         ; Force upper case
    cp  'Y'
    jr  z,WIFI_CONNECT_ME_PWD_Y     ; And tell using encryption
    ld  a,'n'
    call    CHPUT                   ; Overwrite what was typed with 'n'
    xor a                           ; Ok, if here, no pwd, so no encryption
    jr  WIFI_CONNECT_ME_PWD
WIFI_CONNECT_ME_PWD_Y:
    ld  a,'y'
    call    CHPUT                   ; Print 'y'
    ld  a,1                         ; Do not change flags, pwd needed
WIFI_CONNECT_ME_PWD:
    ld  (hl),a                      ; Save if encryption is expected
    push    ix
    pop hl                          ; HL containing the beginning of SSID name
    ld  a,#0d
    call    CHPUT
    ld  a,#0a
    call    CHPUT
    jp  WIFI_CONNECT_AP_PWDQ        ; And the rest is handled like if menu selected
WIFI_CONNECT_ME_BS:
    xor a
    cp  c                           ; Has any data to delete?
    jr  z,WIFI_CONNECT_MANUAL_ENTRY ; No
    ; Yes
    dec hl                          ; Decrement pointer
    dec c                           ; Decrement counter
    ld  a,8                         ; Backspace
    call    CHPUT                   ; Print it
    ld  a,' '                       ; Space
    call    CHPUT                   ; Print it
    ld  a,8                         ; Backspace
    call    CHPUT                   ; Print it
    jr  WIFI_CONNECT_MANUAL_ENTRY   ; Return
WIFI_ME_CHECK_INPUT:
    xor a
    cp  c                           ; Has received any data?
    jr  z,WIFI_CONNECT_MANUAL_ENTRY ; No
    jp  WIFI_CONNECT_ME_0_TERM      ; Yes, so handle SSID input termination

WIFI_CONNECT_SELECTION_OK:
    call    CHPUT                   ; Valid input, print it
    ld  e,'0'
    sub a,e                         ; Get in decimal
    ld  e,a                         ; Back in E
    ; IX has the AP list, A which one has been selected, now our routine will do it
    ld  a,#0d
    call    CHPUT
    ld  a,#0a
    call    CHPUT
    push    ix
    pop hl                          ; put IX in HL
WIFI_CONNECT_AP_SRCH:
    ld  a,e
    or  a
WIFI_CONNECT_AP_SRCH.1:
    jp  z,WIFI_CONNECT_AP_PWDQ
    ld  a,(hl)
    inc hl
    or  a
    jp  nz,WIFI_CONNECT_AP_SRCH.1   ; Find string terminator
    ; Found, jump encryption byte
    inc hl
    dec e                           ; Decrement selection, if 0 we are done
    jp  nz,WIFI_CONNECT_AP_SRCH.1
WIFI_CONNECT_AP_PWDQ:
    ; HL has the address of AP name string
    ld  d,h
    ld  e,l                         ; Save copy in D
    ld  bc,0                        ; BC will have the ap connection data length
WIFI_CONNECT_APSIZE:
    inc bc
    ld  a,(de)
    inc de
    or  a
    jp  nz,WIFI_CONNECT_APSIZE      ; Count size, including zero terminator
    ; Check for encryption
    ld  a,(de)
    or  a
    jp  z,WIFI_CONNECT_SENDCMD      ; If no password requested, good to go
    ; Shoot, need to request password, well, let's do it
    push    hl                      ; Save HL
    ld  hl,MMENU_ASKPWD
    call    PRINTHL                 ; Inform that user need to input PWD
    pop hl                          ; Restore HL
    ld  iy,0                        ; IY will help in backspacing
    ld  ixh,1                       ; Start hidden
WIFI_CONNECT_RCV_PWD:
    call    CHGET
    cp  #1b                         ; ESC?
    jp  z,ESPSETUP                  ; When done, back to main setup
    cp  #08                         ; Backspace?
    jp  z,WIFI_CONNECT_RCV_PWD_BS   ; Check if there is something to erase
    cp  #0d                         ; ENTER?
    jp  z,WIFI_PWD_CHECK_INPUT      ; Check if ok
    cp  #7f                         ; Delete?
    jp  z,WIFI_CONNECT_RCV_PWDH     ; Change password from clear to hidden or vice versa
WIFI_CONNECT_RCV_PWD_STR:
    ; Ok, so it is a digit and store
    ld  (de),a
    ld  a,iyl
    sub 63                          ; 63 chars password limit (WPA2 encryption)
    jr  z,WIFI_CONNECT_RCV_PWD
    ld  a,(de)
    inc bc
    inc de
    inc iy                          ; Increment counters and pointer
    push    af                      ; Save A
    ld  a,ixh
    or  a                           ; If zero, print char, otherwise print *
    jr  z,WIFI_CONNECT_RCV_PWD_CHAR
    pop af
    ld  a,'*'                       ; Print * and keep password hidden
    call    CHPUT
    jp  WIFI_CONNECT_RCV_PWD        ; And back to receiving digits
WIFI_CONNECT_RCV_PWD_CHAR:
    pop af
    cp  32
    jr  nc,WIFI_CONNECT_RCV_CHKPRT2 ; Ok, not below space, but is it delete?
    ld  a,'?'                       ; Prints a question mark
    jr  WIFI_CONNECT_RCV_CHKPRTD
WIFI_CONNECT_RCV_CHKPRT2:
    cp  #7f
    jr  nz,WIFI_CONNECT_RCV_CHKPRTD
    ld  a,'?'                       ; Prints a question mark if it is delete
WIFI_CONNECT_RCV_CHKPRTD:
    call    CHPUT                   ; Print a char
    jp  WIFI_CONNECT_RCV_PWD        ; And back to receiving digits

WIFI_CONNECT_RCV_PWDH:
    ld  a,iyl
    or  iyh
    jp  nz,WIFI_CONNECT_RCV_PWD_STR ; If digits entered, can't change password behavior, so it is a pass phrase char
    xor a
    or  ixh
    ld  ixh,1
    jr  z,WIFI_CONNECT_RCV_PWD      ; Return if it was 0
    ld  ixh,0
    jr  z,WIFI_CONNECT_RCV_PWD      ; Otherwise set to 0 and return

WIFI_CONNECT_RCV_PWD_BS:
    ld  a,iyl
    or  iyh
    jp  z,WIFI_CONNECT_RCV_PWD      ; If no digits entered, nothing to erase
    dec iy                          ; Decrement counter
    dec bc                          ; Decrement counter
    dec de                          ; Decrement pointer
    ld  a,8                         ; Backspace
    call    CHPUT                   ; Print it
    ld  a,' '                       ; Space
    call    CHPUT                   ; Print it
    ld  a,8                         ; Backspace
    call    CHPUT                   ; Print it
    jp  WIFI_CONNECT_RCV_PWD        ; Return

WIFI_PWD_CHECK_INPUT:
    ld  a,iyl
    or  iyh
    jp  z,WIFI_CONNECT_RCV_PWD      ; If no digits entered, no password to send
    ; Otherwise done and ready to send
WIFI_CONNECT_SENDCMD:
    call    WAIT_250MS_AND_THEN_CONTINUE
    push    hl
    ld  HL,MMENU_CONNECTING
    call    PRINTHL
    pop hl
    ; Print AP name
    push    hl
    call    PRINTHLINE              ; Print AP Name
    pop hl
    ; HL has the address of our data, BC the data size, so it is just needed to send the command
    CLEAR_UART
    ld  a,CMD_WIFI_CONNECT
    SEND_DATA
    ld  a,b                         ; Size MSB is in B
    SEND_DATA
    ld  a,c                         ; Size LSB is in c
    SEND_DATA
WIFI_CONNECT_SENDCMDLP:
    ld  a,(hl)
    SEND_DATA
    inc hl
    dec bc
    ld  a,b
    or  c
    jp  nz,WIFI_CONNECT_SENDCMDLP
    ld  hl,600                      ; Wait Up To 10s
    ld  a,CMD_WIFI_CONNECT          ; Our command
    call    WAIT_MENU_QCMD_RESPONSE
    jp  z,WIFI_CONNECT_FAIL
    ld  hl,STR_SENDING_OK_JN        ; Success
    call    PRINTHL
    jp  WAIT_2S_AND_THEN_MAINMENU
WIFI_CONNECT_FAIL:
    ld  hl,STR_SENDING_NOK_JN       ; Failure
    call    PRINTHL
    jp  WAIT_4S_AND_THEN_MAINMENU

INPUT_WFSAP_BAD_INPUT:
    push    bc
    push    de
    push    af
    push    hl
    push    ix
    push    iy
    call    BEEP                    ; Wrong Input, beep
    pop iy
    pop ix
    pop hl
    pop af
    pop de
    pop bc
    jp WIFI_SELECT_AP               ; Return

WIFI_SCAN_NONETWORKS:
    ld  hl,MMENU_SCANN
    call    PRINTHL
    jp  WAIT_4S_AND_THEN_MAINMENU

WIFI_SCAN_TIMEOUT:
    ld  hl,MMENU_SCANF
    call    PRINTHL
    jp  WAIT_4S_AND_THEN_MAINMENU

SET_WIFI_TIMEOUT:
    ld  a,'2'
    call    CHPUT
    call    WAIT_250MS_AND_THEN_CONTINUE
    ld  hl,MMENU_TIMEOUT
    call    PRINTHL                 ; Print Main Timeout message
    call    CHECKTIMEOUT            ; TimeOut is on or off?
    jp  z,WIFI_SET_ALWAYS_ON        ; If 0, always on
    ; Otherwise there is a timeout
    push    hl
    ld hl,MMENU_TIMEOUT_NOTALWAYSON1
    call    PRINTHL
    pop hl
    call    PRINTHL
    ld hl,MMENU_TIMEOUT_NOTALWAYSON2
    call    PRINTHL
    ld  d,0                         ; Count digits
    jr  INPUT_TIMEOUT
WIFI_SET_ALWAYS_ON:
    ld  hl,MMENU_TIMEOUT_ALWAYSON
    call    PRINTHL
    ld  de,(TXTTAB)                 ; We will borrow Basic Program memory area for now...
    ld  ixl,e
    ld  ixh,d                       ; Address in IX
    ld  d,0                         ; Count digits
INPUT_TIMEOUT:
    call    CHGET
    cp  #1b                         ; ESC?
    jp  z,ESPSETUP                  ; When done, back to main setup
    cp  #0d                         ; ENTER?
    jp  z,SET_WIFI_CHECK_INPUT      ; Check if ok
    cp  #08                         ; Backspace?
    jp  z,SET_WIFI_BS_INPUT         ; Check if there is something to erase
    cp  '0'                         ; Check if A is less than 0
    jp  c,INPUT_TIMEOUT_BAD_INPUT   ; if it is, ignore
    cp  '9'+1                       ; Check if a is greater than  9
    jp  nc,INPUT_TIMEOUT_BAD_INPUT  ; If it is, ignore
    ld  (ix+0),a                    ; Save it
    call    CHPUT                   ; It is valid, so print it
    inc d                           ; Increment digit count
    inc ix                          ; Increment pointer
    ld  a,3
    cp  d
    jp  z,SET_WIFI_CHECK_INPUT      ; All we can do is accept up to 3 digits, check if ok
    jp  INPUT_TIMEOUT               ; Not done yet, so continue

INPUT_TIMEOUT_BAD_INPUT:
    call    BEEP                    ; Wrong Input, beep
    jp INPUT_TIMEOUT                ; Return

SET_WIFI_BS_INPUT:
    xor a
    or  d                           ; Counter has any digit?
    jp  z,INPUT_TIMEOUT             ; Nope, so just continue
    dec d                           ; Decrement counter
    dec ix                          ; Decrement pointer
    ld  a,8                         ; Backspace
    call    CHPUT                   ; Print it
    ld  a,' '                       ; Space
    call    CHPUT                   ; Print it
    ld  a,8                         ; Backspace
    call    CHPUT                   ; Print it
    jp  INPUT_TIMEOUT               ; Return

SET_WIFI_CHECK_INPUT:
    xor a
    or  d                           ; Counter has any digits
    jp  z,INPUT_TIMEOUT             ; Nope, so just continue
    ; IX is pointing one position after last digit, so revert
    dec ix
    ld  a,(ix+0)                    ; Digit in A
    sub '0'                         ; Convert it to decimal
    ld  h,0                         ; First digit, so H is 0
    ld  l,a                         ; And L has the digit
    dec d                           ; If digits finished, just set
    jp  z,SET_WIFI_EXECUTE_SET_COMMAND
    dec ix
    ld  a,(ix+0)                    ; Digit in A
    sub '0'                         ; Convert it to decimal
    add a,a                         ; A*2
    ld  c,a                         ; A*2 in C
    add a,a                         ; A*4
    add a,a                         ; A*8
    add a,c                         ; A*10
    ; Up to here, we can get 90 + 9, 99, won't go to H anyway, just add to L
    add a,l                         ; L has the first digit
    ld  l,a                         ; And now L has the two digits
    dec d                           ; If digits finished, just set
    jp  z,SET_WIFI_EXECUTE_SET_COMMAND
    dec ix
    ld  a,(ix+0)                    ; Digit in A
    sub '0'                         ; Convert it to decimal
    add a,a                         ; A*2
    ld  c,a                         ; A*2 in C
    add a,a                         ; A*4
    add a,a                         ; A*8
    add a,c                         ; A*10
    ex  de,hl                       ; Get the two digits results in de
    ld  l,a
    ld  h,0                         ; HL = A*10
    add hl,hl                       ; HL = A*20
    ld  c,l
    ld  b,h                         ; BC = A*20
    add hl,hl                       ; HL = A*40
    add hl,hl                       ; HL = A*80
    add hl,bc                       ; HL = A*100
    add hl,de                       ; HL = three digits result
    ; This was the last digit, up to three
SET_WIFI_EXECUTE_SET_COMMAND:
    jp  SET_ESP_WIFI_TIMEOUT        ; And set and done

;============================
;===  SETUP Menu Routines  ==
;===      NAGLE Menu       ==
;============================
SET_NAGLE:
    ld  a,'1'
    call    CHPUT
    call    WAIT_250MS_AND_THEN_CONTINUE
    ld  hl,MMENU_NAGLE
    call    PRINTHL                 ; Print Main Nagle message
    call    CHECKNAGLE              ; Nagle is on or off?
    jr  nz,NAGLE_IS_ON              ;
    ld  hl,MMENU_NAGLE_OFF          ; Show the menu telling nagle is off
    call    PRINTHL                 ; Print options
SET_NAGLE_WI_ON:
    call    CHGET
    cp  #1b                         ; ESC?
    jp  z,ESPSETUP                  ; When done, back to main setup
    cp  'O'                         ; Toggle Nagle On
    jp  z,SET_NAGLE_ON              ;
    cp  'o'                         ; Toggle Nagle On
    jp  z,SET_NAGLE_ON              ;
    call    BEEP                    ; Wrong Input, beep
    jp  SET_NAGLE_WI_ON             ; And return waiting key

NAGLE_IS_ON:
    ld  hl,MMENU_NAGLE_ON           ; Show the menu telling nagle is on
    call    PRINTHL                 ; Print options
SET_NAGLE_WI_OFF:
    call    CHGET
    cp  #1b                         ; ESC?
    jp  z,ESPSETUP                  ; When done, back to main setup
    cp  'O'                         ; Toggle Nagle Off
    jp  z,SET_NAGLE_OFF             ;
    cp  'o'                         ; Toggle Nagle Off
    jp  z,SET_NAGLE_OFF             ;
    call    BEEP                    ; Wrong Input, beep
    jp  SET_NAGLE_WI_OFF            ; And return waiting key

;============================
;===  SETUP Menu Routines  ==
;===  Auxiliary Functions  ==
;============================
SET_ESP_WIFI_TIMEOUT:
    ex  de,hl
    ld  a,#0d
    call    CHPUT
    ld  a,#0a
    call    CHPUT
    ld  hl,STR_SENDING              ; Indicate it is sending a command
    call    PRINTHL
    CLEAR_UART
    ld  a,CMD_TIMER_SET
    SEND_DATA
    xor a                           ; Size MSB is 0
    SEND_DATA
    ld  a,2                         ; Size LSB is 2
    SEND_DATA
    ld  a,d                         ; Timeout MSB
    SEND_DATA
    ld  a,e                         ; Timeout LSB
    SEND_DATA
    ld  hl,60                       ; Wait Up To 1s
    ld  a,CMD_TIMER_SET             ; Our command
    call    WAIT_MENU_QCMD_RESPONSE
    jp  z,MENU_BAD_END
    ld  hl,STR_SENDING_OK           ; Success
    call    PRINTHL
    jp  WAIT_2S_AND_THEN_MAINMENU

SET_NAGLE_OFF:
    ld  a,'O'
    call    CHPUT
    ld  a,#0d
    call    CHPUT
    ld  a,#0a
    call    CHPUT
    ld  hl,STR_SENDING              ; Indicate it is sending a command
    call    PRINTHL
    CLEAR_UART
    ld  a,CMD_NAGLE_OFF
    SEND_DATA
    ld  hl,60                       ; Wait Up To 1s
    call    WAIT_MENU_QCMD_RESPONSE
    jp  z,MENU_BAD_END
    ld  hl,STR_SENDING_OK           ; Success
    call    PRINTHL
    jp  WAIT_2S_AND_THEN_MAINMENU

STARTWIFISCAN:
    CLEAR_UART
    ld  a,CMD_SCAN_START
    SEND_DATA
    ld  hl,60                       ; Wait Up To 1s
    call    WAIT_MENU_QCMD_RESPONSE
    ret nz                          ; If success return
    ld  a,CR
    call    CHPUT
    ld  a,LF
    call    CHPUT
    jp  MENU_SUB_BAD_END            ; If error, nothing much to do, main menu

SET_NAGLE_ON:
    ld  a,'O'
    call    CHPUT
    ld  a,#0d
    call    CHPUT
    ld  a,#0a
    call    CHPUT
    ld  hl,STR_SENDING              ; Indicate it is sending a command
    call    PRINTHL
    CLEAR_UART
    ld  a,CMD_NAGLE_ON
    SEND_DATA
    ld  hl,60                       ; Wait Up To 1s
    call    WAIT_MENU_QCMD_RESPONSE
    jp  z,MENU_BAD_END
    ld  hl,STR_SENDING_OK           ; Success
    call    PRINTHL
    jp  WAIT_2S_AND_THEN_MAINMENU

WAIT_4S_AND_THEN_MAINMENU:
    ld  a,240                       ; Wait 4 seconds with message on screen
    jr  WAIT_AND_THEN_MAINMENU
WAIT_2S_AND_THEN_MAINMENU:
    ld  a,120                       ; Wait 2 seconds with message on screen
WAIT_AND_THEN_MAINMENU:
    call    WAIT_BEFORE_CONTINUING
    jp  ESPSETUP                    ; When done, back to main setup
WAIT_250MS_AND_THEN_CONTINUE:
    ld  a,15                        ; Wait 250 ms then continue
WAIT_BEFORE_CONTINUING:
    halt
    dec a
    ; If not zero, our time out has not elapsed
    jr  nz,WAIT_BEFORE_CONTINUING
    ret                             ; Time out and continue

; Check Auto Clock
ISCLKAUTO:
    CLEAR_UART
    ld  a,CMD_QUERY_ACLK_SETTINGS
    SEND_DATA
    ld  hl,60                       ; Wait Up To 1s
    ld  de,(TXTTAB)                 ; We will borrow Basic Program memory area for now...
    ld  ixl,e
    ld  ixh,d                       ; address in IX
    call    WAIT_MENU_CMD_RESPONSE
    jp  z,MENU_SUB_BAD_END
    ; Response received, IX+0 and IX+1 has Auto Clock and GMT, A
    ret

; Check what is the current NAGLE setting
CHECKNAGLE:
    CLEAR_UART
    ld  a,CMD_QUERY_ESP_SETTINGS
    SEND_DATA
    ld  hl,60                       ; Wait Up To 1s
    ld  de,(TXTTAB)                 ; We will borrow Basic Program memory area for now...
    ld  ixl,e
    ld  ixh,d                       ; Address in IX
    call    WAIT_MENU_CMD_RESPONSE
    jp  z,MENU_SUB_BAD_END
    ; Response received, nagle is the first one, ON: or OFF:
    ld  a,'O'
    cp  (ix+0)
    jp  nz,MENU_SUB_BAD_END
    ld  a,'N'
    cp  (ix+1)
    jp  nz,CHECK_NAGLE_OFF
    ld  a,':'
    cp  (ix+2)
    jp  nz,MENU_SUB_BAD_END
    or  a                           ; It will make it NZ
    ret
CHECK_NAGLE_OFF:
    ld  a,'F'
    cp  (ix+1)
    jp  nz,MENU_SUB_BAD_END
    ld  a,'F'
    cp  (ix+2)
    jp  nz,MENU_SUB_BAD_END
    ld  a,':'
    cp  (ix+3)
    jp  nz,MENU_SUB_BAD_END
    ; Already has zero, so just ret
    ret

; Check what is the current TIMEOUT setting, return 0 if always on, otherwise there is a timeout
; Will return a zero terminated string @ HL that can be printed
; Will return the value in DE
CHECKTIMEOUT:
    CLEAR_UART
    ld  a,CMD_QUERY_ESP_SETTINGS
    SEND_DATA
    ld  hl,60                       ; Wait Up To 1s
    ld  de,(TXTTAB)                 ; We will borrow Basic Program memory area for now...
    ld  ixl,e
    ld  ixh,d                       ; Address in IX
    call    WAIT_MENU_CMD_RESPONSE
    jp  z,MENU_SUB_BAD_END
    ; Response received, nagle is the first one, ON: or OFF:
    ld  a,':'
    inc ix
    inc ix                          ; Nagle response is two or three bytes long, let's check
    dec bc
    dec bc                          ; Remaining bytes
    cp  (ix+0)
    jp  z,CHECKTIMEOUT.1
    inc ix
    dec bc                          ; Remaining bytes
    cp  (ix+0)
    jp  nz,MENU_SUB_BAD_END         ; If not here, sorry to say it is an error
CHECKTIMEOUT.1:
    ld  a,b
    or  c                           ; All data read?
    jp  z,MENU_SUB_BAD_END          ; If so, sorry to say it is an error
    inc ix                          ; At the first digit
    dec bc                          ; Remaining bytes
    ld  a,b
    or  c                           ; All data read?
    jp  z,MENU_SUB_BAD_END          ; If so, sorry to say it is an error
    push    ix                      ; This is the start of the string, save it
    ld  h,0                         ; No digit so far
    ; It can have up to three digits
CHECKTIMEOUT.2:
    ld  a,':'
    cp  (ix+0)                      ; Check if it is the separator
    jp  z,CHECKTIMEOUT.3            ; If it is routine will follow through
    ld  a,(ix+0)                    ; Get the supposed digit in A
    ld  l,'9'+1
    cp  l
    jp  nc,MENU_SUB_BAD_END_1S      ; If more than '9', sorry to say it is an error
    ld  l,'0'
    cp  l
    jp  c,MENU_SUB_BAD_END_1S       ; If less than '0', sorry to say it is an error
    inc h                           ; It is not, so it is a digit
    ld  a,3
    cp  h
    jp  c,MENU_SUB_BAD_END_1S       ; If more than three digits, sorry to say it is an error
    inc ix                          ; Increase pointer
    dec bc                          ; Decrease remaining
    ld  a,b
    or  c                           ; All data read?
    jp  nz,CHECKTIMEOUT.2           ; Not, so rinse and repeat
CHECKTIMEOUT.3:
    ld  (ix+0),0                    ; Null terminate string value
    dec ix
    ld  a,(ix+0)                    ; 1st Digit in A
    sub '0'                         ; Convert it to decimal value
    ld  e,a
    ld  d,0                         ; DE has first digit
    dec h                           ; Decrement digit counter
    jr  z,CHECKTIMEOUT.END          ; If all digits, done
    ; Now second digit, multiply it by 10 and add to E, even if 90 + 9, still fits E
    dec ix
    ld  a,(ix+0)                    ; 2nd Digit
    sub '0'                         ; Convert it to decimal value
    add a,a                         ; A has *2
    ld  c,a                         ; C has *2
    add a,a                         ; A has *4
    add a,a                         ; A has *8
    add a,c                         ; A has *10
    add a,e                         ; A has two digits result
    ld  e,a                         ; Back to E, DE has two digits results
    dec h                           ; Decrement digit counter
    jr  z,CHECKTIMEOUT.END          ; If all digits, done
    ; Now Third digit, multiply it by 100 and add to DE
    dec ix
    ld  a,(ix+0)                    ; 3rd Digit
    sub '0'                         ; Convert it to decimal value
    add a,a                         ; A has *2
    ld  c,a                         ; C has *2
    add a,a                         ; A has *4
    add a,a                         ; A has *8
    add a,c                         ; A has *10
    ld  h,0
    ld  l,a                         ; HL has *10
    add hl,hl                       ; HL has *20
    ld  b,h
    ld  c,l                         ; BC has *20
    add hl,hl                       ; HL has *40
    add hl,hl                       ; HL has *80
    add hl,bc                       ; HL has *100
    add hl,de                       ; HL has three digit value
    ex  de,hl                       ; now in DE
CHECKTIMEOUT.END:
    pop hl                          ; Restore address of string version of time count
    ld  a,d
    or  e                           ; Set zero flag according to the time out set
    ret

MENU_SUB_BAD_END_1S:
    pop af                          ; 1 register was stacked, pop it
MENU_SUB_BAD_END:
    pop af                          ; It was a sub, so clear stack
MENU_BAD_END:
    ld  hl,STR_SENDING_FAIL         ; error message
    call    PRINTHL
    jp  WAIT_2S_AND_THEN_MAINMENU

; WAIT an ESP quick command Response
; Inputs:
; A -> Command Code
; HL -> Timeout
;
; Returns:
; Flag Z is zero if failure, non zero if success
;
; Affect:
; AF and HL
;
WAIT_MENU_QCMD_RESPONSE:
    push    de
    ld  d,a                         ; Command to wait in D
WAIT_MENU_QCMD_RESPONSE_ST1:
    LOAD_STS_PORT_IN_A
    bit 5,a                         ; If nz Port #07 is not available
    jp  nz,WAIT_MENU_QCMD_RESPONSE_END_NOK
    bit 0,a                         ; If nz has data
    jr  nz,WAIT_MENU_QCMD_RESPONSE_ST1.1
    call    HLTIMEOUT
    jr  nz,WAIT_MENU_QCMD_RESPONSE_ST1
    jp  WAIT_MENU_QCMD_RESPONSE_END ; If time out waiting, return
WAIT_MENU_QCMD_RESPONSE_ST1.1:
    ; nz, check the data
    RECEIVE_DATA
    cp  d                           ; Is response of our command?
    jr  nz,WAIT_MENU_QCMD_RESPONSE_ST1
    ; Now get return code, if return code other than 0, it is failure, otherwise success
WAIT_MENU_QCMD_RESPONSE_RC:
    CHECK_DATA
    jr  nz,WAIT_MENU_QCMD_RESPONSE_RC.1
    call    HLTIMEOUT
    jr  nz,WAIT_MENU_QCMD_RESPONSE_RC
    jp  WAIT_MENU_QCMD_RESPONSE_END ; If time-out waiting, return
WAIT_MENU_QCMD_RESPONSE_RC.1:
    RECEIVE_DATA
    or  a                           ; 0?
    ; If not, done
    jp  nz,WAIT_MENU_QCMD_RESPONSE_END_NOK
WAIT_MENU_QCMD_RESPONSE_END_OK:
    ld  a,1
    or  a                           ; NZ to indicate success
WAIT_MENU_QCMD_RESPONSE_END:
    pop de
    ret
WAIT_MENU_QCMD_RESPONSE_END_NOK:
    ld  hl,0
    xor a
    pop de
    ret

; WAIT an ESP regular command Response
; Inputs:
; A -> Command Code
; HL -> Timeout
; IX -> Where to store response
;
; Returns:
; Flag Z is zero if failure, non zero if success
; BC is the response size
;
; Affect:
; AF , BC and HL
WAIT_MENU_CMD_RESPONSE:
    push    de
    push    ix
    ld  d,a                         ; Command to wait in D
WAIT_MENU_CMD_RESPONSE_ST1:
    LOAD_STS_PORT_IN_A
    bit 5,a                         ; If nz Port #07 is not available
    jp  nz,WAIT_MENU_CMD_RESPONSE_END_NOK
    bit 0,a                         ; If nz has data
    jr  nz,WAIT_MENU_CMD_RESPONSE_ST1.1
    call    HLTIMEOUT
    jr  nz,WAIT_MENU_CMD_RESPONSE_ST1
    jp  WAIT_MENU_CMD_RESPONSE_END  ; If time out waiting, return
WAIT_MENU_CMD_RESPONSE_ST1.1:
    ; nz, check the data
    RECEIVE_DATA
    cp  d                           ; Is response of our command?
    jr  nz,WAIT_MENU_CMD_RESPONSE_ST1
    ; Now get return code, if return code other than 0, it is finished
WAIT_MENU_CMD_RESPONSE_RC:
    CHECK_DATA
    jr  nz,WAIT_MENU_CMD_RESPONSE_RC.1
    call    HLTIMEOUT
    jr  nz,WAIT_MENU_CMD_RESPONSE_RC
    jp  WAIT_MENU_CMD_RESPONSE_END  ; If time out waiting, return
WAIT_MENU_CMD_RESPONSE_RC.1:
    RECEIVE_DATA
    or  a                           ; 0?
    ; If not, done
    jp  nz,WAIT_MENU_CMD_RESPONSE_END_NOK
    ; Next two bytes are size bytes, save it to BC
WAIT_MENU_CMD_RESPONSE_ST2A:
    CHECK_DATA
    jr  nz,WAIT_MENU_CMD_RESPONSE_ST2A.1
    call    HLTIMEOUT
    jr  nz,WAIT_MENU_CMD_RESPONSE_ST2A
    jp  WAIT_MENU_CMD_RESPONSE_END  ; If time out waiting, return
WAIT_MENU_CMD_RESPONSE_ST2A.1:
    RECEIVE_DATA
    ld  b,a
WAIT_MENU_CMD_RESPONSE_ST2B:
    CHECK_DATA
    jr  nz,WAIT_MENU_CMD_RESPONSE_ST2B.1
    call    HLTIMEOUT
    jr  nz,WAIT_MENU_CMD_RESPONSE_ST2B
    jp  WAIT_MENU_CMD_RESPONSE_END  ; If time out waiting, return
WAIT_MENU_CMD_RESPONSE_ST2B.1:
    RECEIVE_DATA
    ld  c,a
    or  b                           ; Zero size in response?
    jr  z,WAIT_MENU_CMD_RESPONSE_END_OK
    ld  d,b
    ld  e,c                         ; Copy to DE
    ; Now loop getting the data until received everything or time-out
WAIT_MENU_CMD_RESPONSE_GET_DATA:
    CHECK_DATA
    jr  nz,WAIT_MENU_CMD_RESPONSE_GET_DATA.1
    call    HLTIMEOUT
    jr  nz,WAIT_MENU_CMD_RESPONSE_GET_DATA
    jp  WAIT_MENU_CMD_RESPONSE_END  ; If time out waiting, return
WAIT_MENU_CMD_RESPONSE_GET_DATA.1:
    RECEIVE_DATA            ; Get data
    ld  (ix+0),a                    ; Put it in the buffer
    inc ix                          ; Increment pointer
    dec de                          ; Decrement counter
    ld  a,d
    or  e                           ; Is counter 0?
    jr  nz,WAIT_MENU_CMD_RESPONSE_GET_DATA
WAIT_MENU_CMD_RESPONSE_END_OK:
    ld  a,1
    or  a                           ; NZ to indicate success
    pop ix
    pop de
    ret
WAIT_MENU_CMD_RESPONSE_END:
    ld  b,#FF
    pop ix
    pop de
    ret
WAIT_MENU_CMD_RESPONSE_END_NOK:
    ld  hl,0
    ld  b,a                         ; Get result in B, 0xFF for time-out, otherwise was an error return code
    xor a
    pop ix
    pop de
    ret

; WAIT an ESP Wi-Fi Scan command Response
; Inputs:
; A -> Command Code
; HL -> Timeout
; IX -> Where to store response
;
; Returns:
; Flag Z is zero if failure, non zero if success
; A is the number of access points scanned
;
; Response is stored as:
; Access Point SSID zero terminated and after first 0
; 0 if Open otherwise requires a password to join
; And this repeats...
;
; Affect:
; AF , BC and HL
;
WAIT_MENU_SCMD_RESPONSE:
    push    de
    push    ix
    ld  d,a                         ; Command to wait in D
WAIT_MENU_SCMD_RESPONSE_ST1:
    LOAD_STS_PORT_IN_A
    bit 5,a                         ; If nz Port #07 is not available
    jp  nz,WAIT_MENU_SCMD_RESPONSE_END_NOK
    bit 0,a                         ; If nz has data
    jr  nz,WAIT_MENU_SCMD_RESPONSE_ST1.1
    call    HLTIMEOUT
    jr  nz,WAIT_MENU_SCMD_RESPONSE_ST1
    jp  WAIT_MENU_SCMD_RESPONSE_END ; If time out waiting, return
WAIT_MENU_SCMD_RESPONSE_ST1.1:
    ; nz, check the data
    RECEIVE_DATA
    cp  d                           ; Is response of our command?
    jr  nz,WAIT_MENU_SCMD_RESPONSE_ST1
    ; Now get return code, if return code other than 0, it is finished
WAIT_MENU_SCMD_RESPONSE_RC:
    CHECK_DATA
    jr  nz,WAIT_MENU_SCMD_RESPONSE_RC.1
    call    HLTIMEOUT
    jr  nz,WAIT_MENU_SCMD_RESPONSE_RC
    jp  WAIT_MENU_SCMD_RESPONSE_END ; If time out waiting, return
WAIT_MENU_SCMD_RESPONSE_RC.1:
    RECEIVE_DATA
    or  a                           ; 0?
    ; If not, done
    jp  nz,WAIT_MENU_SCMD_RESPONSE_END_NOK
    ; Next byte is how many access points are available
WAIT_MENU_SCMD_RESPONSE_ST2A:
    CHECK_DATA
    jr  nz,WAIT_MENU_SCMD_RESPONSE_ST2A.1
    call    HLTIMEOUT
    jr  nz,WAIT_MENU_SCMD_RESPONSE_ST2A
    jp  WAIT_MENU_SCMD_RESPONSE_END ; If time out waiting, return
WAIT_MENU_SCMD_RESPONSE_ST2A.1:
    RECEIVE_DATA
    ld  b,a                         ; Save in B
    ld  c,a                         ; And C as well
    ; Now should loop this until c is 0, c will control access point received count
WAIT_MENU_SCMD_RESPONSE_ST2B:
    CHECK_DATA
    jr  nz,WAIT_MENU_SCMD_RESPONSE_ST2B.1
    call    HLTIMEOUT
    jr  nz,WAIT_MENU_SCMD_RESPONSE_ST2B
    jp  WAIT_MENU_SCMD_RESPONSE_END ; If time out waiting, return
WAIT_MENU_SCMD_RESPONSE_ST2B.1:
    RECEIVE_DATA
    ld  (ix+0),a
    inc ix                          ; Increment pointer
    or  a                           ; Terminator of AP Name?
    jr  nz,WAIT_MENU_SCMD_RESPONSE_ST2B
    ; Get encryption
WAIT_MENU_SCMD_RESPONSE_GET_ENC:
    CHECK_DATA
    jr  nz,WAIT_MENU_SCMD_RESPONSE_GET_ENC.1
    call    HLTIMEOUT
    jr  nz,WAIT_MENU_SCMD_RESPONSE_GET_ENC
    jp  WAIT_MENU_SCMD_RESPONSE_END  ; If time out waiting, return
WAIT_MENU_SCMD_RESPONSE_GET_ENC.1:
    RECEIVE_DATA            ; Get data
    sub 'O'                         ; If O, open, will be 0, otherwise, will be notzero
    ld  (ix+0),a                    ; Put it in the buffer
    inc ix                          ; Increment pointer
    dec c                           ; Decrement counter
    xor a
    or  c                           ; Is counter 0?
    ; If not continue getting more SSIDs
    jr  nz,WAIT_MENU_SCMD_RESPONSE_ST2B
    ; It is zero, so, done
WAIT_MENU_SCMD_RESPONSE_END_OK:
    ld  a,1
    or  a                           ; NZ to indicate success
    ld  a,b                         ; Number of APs in A
WAIT_MENU_SCMD_RESPONSE_END:
    pop ix
    pop de
    ret
WAIT_MENU_SCMD_RESPONSE_END_NOK:
    ld  hl,0
    ld  b,a                         ; Return code in B
    xor a
    pop ix
    pop de
    ret

; This routine will check if HL is 0, if it is, will return immediatelly
; If it is not, will decrease HL value and halt (wait one interrupt)
HLTIMEOUT:
    ld  a,h
    or  l
    ret z
    dec hl
    halt
    ret

; Routine to print the string addressed by HL
PRINTHL:
    ld  a,(hl)
    or  a
    ret z                           ; When string is finished, done!
    call    CHPUT
    inc hl
    jp  PRINTHL

; Routine to print the string addressed by HL on a line, if exceeding it, ends with ..
PRINTHLINE:
    push    bc
    ld  b,24
PHLINEL:
    ld  a,(hl)
    or  a
    jr  z,PHLINESPC                 ; When string is finished, done!
    call    CHPUT
    inc hl
    djnz    PHLINEL
    ld  a,GOLEFT
    call    CHPUT
    call    CHPUT
    ld  a,1
    call    CHPUT
    ld  a,91
    call    CHPUT
    ld  a,' '
    call    CHPUT
    jr  PHLINELR
PHLINESPC:
    ld  a,' '
    call    CHPUT
    djnz    PHLINESPC
PHLINELR:
    ld  a,GOLEFT
    call    CHPUT
    call    CHPUT
    pop bc
    ret

;===============================
;===  HTIM_I hook execution  ===
;===============================
DO_HTIMI:
    push    af                      ; HTIM hook -> need to keep A value
    call    GETCOUNTER              ; Counter in hl
    ld  a,l
    or  h                           ; In this operation, check if HL is o
    jr  z,DO_HTIMI_END              ; If it is, nothing to do
    dec hl                          ; Otherwise decrement it
    call    SETCOUNTER              ; And save it
DO_HTIMI_END:
    call    GETSLT
    ; Slot in A, now get the address of our counter
    call    GETMEMPOINTER
    ; HL has the address of our memory area, and there is where we should jump
    pop af                          ; Restore original A value
    jp  (hl)

;===============================
;===  EXTBIO hook execution  ===
;===============================
DO_EXTBIO:
    push    hl
    push    bc
    push    af
    ld  a,d
    cp  #22
    jr  nz,JUMP_OLD
    cp  e
    jr  nz,JUMP_OLD

    ; Check API ID
    ld  hl,UNAPI_ID
    ld  de,ARG
LOOP:
    ld  a,(de)
    call    TOUPPER
    cp  (hl)
    jr  nz,JUMP_OLD2
    inc hl
    inc de
    or  a
    jr  nz,LOOP

    ; A=255: Jump to old hook

    pop af
    push    af
    inc a
    jr  z,JUMP_OLD2

    ; A=0: B=B+1 and jump to old hook

    call    GETSLT
    call    GETWRK
    pop af
    pop bc
    or  a
    jr  nz,DO_EXTBIO2
    inc b
    ex  (sp),hl
    ld  de,#2222
    ret

DO_EXTBIO2:
    ; A=1: Return A=Slot, B=Segment, HL=UNAPI entry address

    dec a
    jr  nz,DO_EXTBIO3
    pop hl
    call    GETSLTT                 ; GETSLTT is GETSLT that checks if our memory area @ HIMEM has been allocated, if not, allocate it
    ld  b,#FF
    ld  hl,UNAPI_ENTRY
    ld  de,#2222
    ret

    ; A>1: A=A-1, and jump to old hook

DO_EXTBIO3:                         ; A=A-1 already done
    ex  (sp),hl
    ld  de,#2222
    ret


; Jump here to execute old EXTBIO code
JUMP_OLD2:
    ld  de,#2222
JUMP_OLD:                           ; Assumes "push hl,bc,af" done
    push    de
    call    GETSLT
    call    GETWRK
    pop de
    pop af
    pop bc
    ex  (sp),hl
    ret

;====================================
;===  Functions entry point code  ===
;====================================
UNAPI_ENTRY:
    ei
    push    hl
    push    af
    ld  hl,FN_TABLE
    bit 7,a

    if  MAX_IMPFN >= 128

    jr  z,IS_STANDARD
    ld  hl,IMPFN_TABLE
    and %01111111
    cp  MAX_IMPFN-128
    jr  z,OK_FNUM
    jr  nc,UNDEFINED
IS_STANDARD:

    else

    jr  nz,UNDEFINED

    endif

    cp  MAX_FN
    jr  z,OK_FNUM
    jr  nc,UNDEFINED

OK_FNUM:
    add a,a
    push    de
    ld  e,a
    ld  d,0
    add hl,de
    pop de

    ld  a,(hl)
    inc hl
    ld  h,(hl)
    ld  l,a

    pop af
    ex  (sp),hl
    ret

; Undefined function: return with registers unmodified
UNDEFINED:
    pop af
    pop hl
    ret

;===================================
;===  Functions addresses table  ===
;===================================
;--- Implementation-specific routines addresses table

    if  MAX_IMPFN >= 128

IMPFN_TABLE:
FN_128:                 dw  FN_DUMMY

    endif

FN_TABLE:
FN_0:                   dw  UNAPI_GET_INFO
FN_1:                   dw  TCPIP_GET_CAPAB
FN_2:                   dw  TCPIP_GET_IPINFO
FN_3:                   dw  TCPIP_NET_STATE
; TCPIP_SEND_ECHO not going to be implemented, ESP do not support ping like UNAPI specify
FN_4:                   dw  FN_NOT_IMP
; TCPIP_RCV_ECHO not going to be implemented as SEND_ECHO is not implemented
FN_5:                   dw  FN_NOT_IMP
FN_6:                   dw  TCPIP_DNS_Q
FN_7:                   dw  TCPIP_DNS_S
FN_8:                   dw  TCPIP_UDP_OPEN
FN_9:                   dw  TCPIP_UDP_CLOSE
FN_10:                  dw  TCPIP_UDP_STATE
FN_11:                  dw  TCPIP_UDP_SEND
FN_12:                  dw  TCPIP_UDP_RCV
FN_13:                  dw  TCPIP_TCP_OPEN
FN_14:                  dw  TCPIP_TCP_CLOSE
FN_15:                  dw  TCPIP_TCP_ABORT
FN_16:                  dw  TCPIP_TCP_STATE
FN_17:                  dw  TCPIP_TCP_SEND
FN_18:                  dw  TCPIP_TCP_RCV
; TCPIP_TCP_FLUSH makes no sense as we do not use buffers to send, any buffer is internal to ESP and we can't delete
FN_19:                  dw  FN_NOT_IMP
; TCPIP_RAW_OPEN not going to be implemented, ESP do not support RAW connections
FN_20:                  dw  FN_NOT_IMP
; TCPIP_RAW_CLOSE not going to be implemented, ESP do not support RAW connections
FN_21:                  dw  FN_NOT_IMP
; TCPIP_RAW_STATE not going to be implemented, ESP do not support RAW connections
FN_22:                  dw  FN_NOT_IMP
; TCPIP_RAW_SEND not going to be implemented, ESP do not support RAW connections
FN_23:                  dw  FN_NOT_IMP
; TCPIP_RAW_RCV not going to be implemented, ESP do not support RAW connections
FN_24:                  dw  FN_NOT_IMP
FN_25:                  dw  TCPIP_CONFIG_AUTOIP
FN_26:                  dw  TCPIP_CONFIG_IP
FN_27:                  dw  TCPIP_CONFIG_TTL
FN_28:                  dw  TCPIP_CONFIG_PING
; TCPIP_WAIT not needed for our implementation
FN_29:                  dw  END_OK

;========================
;===  Functions code  ===
;========================
FN_NOT_IMP:
    ld  a,ERR_NOT_IMP
    ret

END_OK:
    xor a
    ret

; Most functions do not have special handling on time out and can use this.
; If there is a need to retry sending or receiving on time-out, then a custom
; time-out function must be done, check the examples of UDP and TCP receive
TCPIP_GENERIC_CHECK_TIME_OUT:
    ; Save registers other than AF
    push bc
    push de
    push hl
    call    GETCOUNTER
    ld  a,l
    or  h
    ; Restore registers, we are returning
    pop hl
    pop de
    pop bc
    ret nz
    ; Ok, timeout...
    pop af                          ; Get return address of who called this out of the stack
    ld  a,ERR_INV_OPER
    ret                             ; and return the function itself

;========================
;===  UNAPI_GET_INFO  ===
;========================
; Obtain the implementation name and version.
;
;    Input:  A  = 0
;    Output: HL = Descriptive string for this implementation, on this slot, zero terminated
;            DE = API version supported, D.E
;            BC = This implementation version, B.C.
;            A  = 0 and Cy = 0
UNAPI_GET_INFO:
    ld  bc,256*ROM_V_P+ROM_V_S
    ld  de,256*API_V_P+API_V_S
    ld  hl,APIINFO
    xor a
    ret

;=========================
;===  TCPIP_GET_CAPAB  ===
;=========================
; Get information about the TCP/IP capabilities and features.
;
;    Input:  A = 1
;            B = Index of information block to retrieve:
;                1: Capabilities and features flags, link level protocol
;                2: Connection pool size and status
;                3: Maximum datagram size allowed
;                4: Second set of capabilities and features flags
;    Output: A = Error code
;        When information block 1 requested:
;            HL = Capabilities flags
;            DE = Features flags
;            B  = Link level protocol used
;        When information block 2 requested:
;            B = Maximum simultaneous TCP connections supported
;            C = Maximum simultaneous UDP connections supported
;            D = Free TCP connections currently available
;            E = Free UDP connections currently available
;            H = Maximum simultaneous raw IP connections supported
;            L = Free raw IP connections currently available
;        When information block 3 requested:
;            HL = Maximum incoming datagram size supported
;            DE = Maximum outgoing datagram size supported
;        When information block 4 requested:
;            HL = Second set of capabilities flags
;            DE = Second set of features flags (currently unused, always zero)
TCPIP_GET_CAPAB:
    SEND_DATA                       ; Send the command
    xor a
    SEND_DATA                       ; Send the command size msb
    inc a
    SEND_DATA                       ; Send the command size lsb
    ld  a,b
    call    SETBYTE                 ; Save it, we are going to need it later
    SEND_DATA                       ; Send the parameter

    ; Now wait up to 120 ticks to get response
    ld  hl,120
    call    SETCOUNTER
TCPIP_GET_CAPAB_ST1:
    CHECK_DATA
    jr  nz,TCPIP_GET_CAPAB_ST1.1
    call    TCPIP_GENERIC_CHECK_TIME_OUT
    jr  TCPIP_GET_CAPAB_ST1
TCPIP_GET_CAPAB_ST1.1:
    ; nz, check the data
    RECEIVE_DATA
    cp  1                           ; Is response of our command?
    jr  nz,TCPIP_GET_CAPAB_ST1
    ; Now get return code, if return code other than 0, it is finished
TCPIP_GET_CAPAB_RC:
    CHECK_DATA
    jr  nz,TCPIP_GET_CAPAB_RC.1
    call    TCPIP_GENERIC_CHECK_TIME_OUT
    jr  TCPIP_GET_CAPAB_RC
TCPIP_GET_CAPAB_RC.1:
    ; nz, discard
    RECEIVE_DATA
    or  a                           ; 0?
    ret nz                          ; If not, done

    ; Next two bytes are return code and size bytes, don't care
    ld  b,2
TCPIP_GET_CAPAB_ST2:
    CHECK_DATA
    jr  nz,TCPIP_GET_CAPAB_ST2.1
    call    TCPIP_GENERIC_CHECK_TIME_OUT
    jr  TCPIP_GET_CAPAB_ST2
TCPIP_GET_CAPAB_ST2.1:
    ; Nz, discard
    RECEIVE_DATA
    dec b
    jr  nz,TCPIP_GET_CAPAB_ST2

    ; Now check if block 1, 2 or 3
    call    GETBYTE                 ; Get the parameter we saved at the start
    dec a
    jp  z,TCPIP_GET_CAPAB_BLK1      ; 1
    dec a
    jp  z,TCPIP_GET_CAPAB_BLK2      ; 2
    dec a
    jp  z,TCPIP_GET_CAPAB_BLK3      ; 3
    ; Else, only block four, same as block 1
    jp  TCPIP_GET_CAPAB_BLK1        ; 1
    ; Block 3 Handling, we will receive L, H, E and D
TCPIP_GET_CAPAB_BLK3:
TCPIP_GET_CAPAB_BLK3_ST1:
    CHECK_DATA
    jr  nz,TCPIP_GET_CAPAB_BLK3_ST1.1
    call    TCPIP_GENERIC_CHECK_TIME_OUT
    jr  TCPIP_GET_CAPAB_BLK3_ST1
TCPIP_GET_CAPAB_BLK3_ST1.1:
    ; nz, get it
    RECEIVE_DATA
    ld  l,a
TCPIP_GET_CAPAB_BLK3_ST2:
    CHECK_DATA
    jr  nz,TCPIP_GET_CAPAB_BLK3_ST2.1
    call    TCPIP_GENERIC_CHECK_TIME_OUT
    jr  TCPIP_GET_CAPAB_BLK3_ST2
TCPIP_GET_CAPAB_BLK3_ST2.1:
    ; nz, get it
    RECEIVE_DATA
    ld  h,a
TCPIP_GET_CAPAB_BLK3_ST3:
    CHECK_DATA
    jr  nz,TCPIP_GET_CAPAB_BLK3_ST3.1
    call    TCPIP_GENERIC_CHECK_TIME_OUT
    jr  TCPIP_GET_CAPAB_BLK3_ST3
TCPIP_GET_CAPAB_BLK3_ST3.1:
    ; nz, get it
    RECEIVE_DATA
    ld  e,a
TCPIP_GET_CAPAB_BLK3_ST4:
    CHECK_DATA
    jr  nz,TCPIP_GET_CAPAB_BLK3_ST4.1
    call    TCPIP_GENERIC_CHECK_TIME_OUT
    jr  TCPIP_GET_CAPAB_BLK3_ST4
TCPIP_GET_CAPAB_BLK3_ST4.1:
    ; nz, get it
    RECEIVE_DATA
    ld  d,a
    ; Done
    xor a
    ret

TCPIP_GET_CAPAB_BLK2:
    ; Block 2 Handling, we will receive B, C, D, E, H, L
TCPIP_GET_CAPAB_BLK2_ST1:
    CHECK_DATA
    jr  nz,TCPIP_GET_CAPAB_BLK2_ST1.1
    call    TCPIP_GENERIC_CHECK_TIME_OUT
    jr  TCPIP_GET_CAPAB_BLK2_ST1
TCPIP_GET_CAPAB_BLK2_ST1.1:
    ; nz, get it
    RECEIVE_DATA
    ld  b,a
TCPIP_GET_CAPAB_BLK2_ST2:
    CHECK_DATA
    jr  nz,TCPIP_GET_CAPAB_BLK2_ST2.1
    call    TCPIP_GENERIC_CHECK_TIME_OUT
    jr  TCPIP_GET_CAPAB_BLK2_ST2
TCPIP_GET_CAPAB_BLK2_ST2.1:
    ; nz, get it
    RECEIVE_DATA
    ld  c,a
TCPIP_GET_CAPAB_BLK2_ST3:
    CHECK_DATA
    jr  nz,TCPIP_GET_CAPAB_BLK2_ST3.1
    call    TCPIP_GENERIC_CHECK_TIME_OUT
    jr  TCPIP_GET_CAPAB_BLK2_ST3
TCPIP_GET_CAPAB_BLK2_ST3.1:
    ; nz, get it
    RECEIVE_DATA
    ld  d,a
TCPIP_GET_CAPAB_BLK2_ST4:
    CHECK_DATA
    jr  nz,TCPIP_GET_CAPAB_BLK2_ST4.1
    call    TCPIP_GENERIC_CHECK_TIME_OUT
    jr  TCPIP_GET_CAPAB_BLK2_ST4
TCPIP_GET_CAPAB_BLK2_ST4.1:
    ; nz, get it
    RECEIVE_DATA
    ld  e,a
TCPIP_GET_CAPAB_BLK2_ST5:
    CHECK_DATA
    jr  nz,TCPIP_GET_CAPAB_BLK2_ST5.1
    call    TCPIP_GENERIC_CHECK_TIME_OUT
    jr  TCPIP_GET_CAPAB_BLK2_ST5
TCPIP_GET_CAPAB_BLK2_ST5.1:
    ; nz, get it
    RECEIVE_DATA
    ld  h,a
TCPIP_GET_CAPAB_BLK2_ST6:
    CHECK_DATA
    jr  nz,TCPIP_GET_CAPAB_BLK2_ST6.1
    call    TCPIP_GENERIC_CHECK_TIME_OUT
    jr  TCPIP_GET_CAPAB_BLK2_ST6
TCPIP_GET_CAPAB_BLK2_ST6.1:
    ; nz, get it
    RECEIVE_DATA
    ld  l,a
    ; Done
    xor a
    ret

TCPIP_GET_CAPAB_BLK1:
    ; Block 1 Handling, we will receive L, H, E, D and B
TCPIP_GET_CAPAB_BLK1_ST1:
    CHECK_DATA
    jr  nz,TCPIP_GET_CAPAB_BLK1_ST1.1
    call    TCPIP_GENERIC_CHECK_TIME_OUT
    jr  TCPIP_GET_CAPAB_BLK1_ST1
TCPIP_GET_CAPAB_BLK1_ST1.1:
    ; nz, get it
    RECEIVE_DATA
    ld  l,a
TCPIP_GET_CAPAB_BLK1_ST2:
    CHECK_DATA
    jr  nz,TCPIP_GET_CAPAB_BLK1_ST2.1
    call    TCPIP_GENERIC_CHECK_TIME_OUT
    jr  TCPIP_GET_CAPAB_BLK1_ST2
TCPIP_GET_CAPAB_BLK1_ST2.1:
    ; nz, get it
    RECEIVE_DATA
    ld  h,a
TCPIP_GET_CAPAB_BLK1_ST3:
    CHECK_DATA
    jr  nz,TCPIP_GET_CAPAB_BLK1_ST3.1
    call    TCPIP_GENERIC_CHECK_TIME_OUT
    jr  TCPIP_GET_CAPAB_BLK1_ST3
TCPIP_GET_CAPAB_BLK1_ST3.1:
    ; nz, get it
    RECEIVE_DATA
    ld  e,a
TCPIP_GET_CAPAB_BLK1_ST4:
    CHECK_DATA
    jr  nz,TCPIP_GET_CAPAB_BLK1_ST4.1
    call    TCPIP_GENERIC_CHECK_TIME_OUT
    jr  TCPIP_GET_CAPAB_BLK1_ST4
TCPIP_GET_CAPAB_BLK1_ST4.1:
    ; nz, get it
    RECEIVE_DATA
    ld  d,a
TCPIP_GET_CAPAB_BLK1_ST5:
    CHECK_DATA
    jr  nz,TCPIP_GET_CAPAB_BLK1_ST5.1
    call    TCPIP_GENERIC_CHECK_TIME_OUT
    jr  TCPIP_GET_CAPAB_BLK1_ST5
TCPIP_GET_CAPAB_BLK1_ST5.1:
    ; nz, get it
    RECEIVE_DATA
    ld  b,a
    ; Done
    xor a
    ret

;==========================
;===  TCPIP_GET_IPINFO  ===
;==========================
;Get IP address.
;
;Input:  A = 2
;        B = Index of address to obtain:
;            1: Local IP address
;            2: Peer IP address
;            3: Subnet mask
;            4: Default gateway
;            5: Primary DNS server IP address
;            6: Secondary DNS server IP address
;Output: A = Error code
;        L.H.E.D = Requested address
TCPIP_GET_IPINFO:
    SEND_DATA                       ; Send the command
    xor a
    SEND_DATA                       ; Send the command size msb
    inc a
    SEND_DATA                       ; Send the command size lsb
    ld  a,b
    SEND_DATA

    ; Now wait up to 600 ticks to get response
    ld  hl,600
    call    SETCOUNTER
TCPIP_GET_IPINFO_ST1:
    CHECK_DATA
    jr  nz,TCPIP_GET_IPINFO_ST1.1
    call    TCPIP_GENERIC_CHECK_TIME_OUT
    jr  TCPIP_GET_IPINFO_ST1
TCPIP_GET_IPINFO_ST1.1:
    ; nz, check the data
    RECEIVE_DATA
    cp  2                           ; Is response of our command?
    jr  nz,TCPIP_GET_IPINFO_ST1
    ; now get return code, if return code other than 0, it is finished
TCPIP_GET_IPINFO_RC:
    CHECK_DATA
    jr  nz,TCPIP_GET_IPINFO_RC.1
    call    TCPIP_GENERIC_CHECK_TIME_OUT
    jr  TCPIP_GET_IPINFO_RC
TCPIP_GET_IPINFO_RC.1:
    ; nz, discard
    RECEIVE_DATA
    or  a                           ; 0?
    ret nz                          ; if not, done

    ; next two bytes are return code and size bytes, don't care, it is 4
    ld  b,2
TCPIP_GET_IPINFO_ST2:
    CHECK_DATA
    jr  nz,TCPIP_GET_IPINFO_ST2.1
    call    TCPIP_GENERIC_CHECK_TIME_OUT
    jr  TCPIP_GET_IPINFO_ST2
TCPIP_GET_IPINFO_ST2.1:
    ; nz, discard
    RECEIVE_DATA
    dec b
    jr  nz,TCPIP_GET_IPINFO_ST2

    ; now just get the 4 bytes IP and order it in L, H, E and D
TCPIP_GET_IPINFO_IP_ST1:
    CHECK_DATA
    jr  nz,TCPIP_GET_IPINFO_IP_ST1.1
    call    TCPIP_GENERIC_CHECK_TIME_OUT
    jr  TCPIP_GET_IPINFO_IP_ST1
TCPIP_GET_IPINFO_IP_ST1.1:
    ; nz, get it
    RECEIVE_DATA
    ld  l,a
TCPIP_GET_IPINFO_IP_ST2:
    CHECK_DATA
    jr  nz,TCPIP_GET_IPINFO_IP_ST2.1
    call    TCPIP_GENERIC_CHECK_TIME_OUT
    jr  TCPIP_GET_IPINFO_IP_ST2
TCPIP_GET_IPINFO_IP_ST2.1:
    ; nz, get it
    RECEIVE_DATA
    ld  h,a
TCPIP_GET_IPINFO_IP_ST3:
    CHECK_DATA
    jr  nz,TCPIP_GET_IPINFO_IP_ST3.1
    call    TCPIP_GENERIC_CHECK_TIME_OUT
    jr  TCPIP_GET_IPINFO_IP_ST3
TCPIP_GET_IPINFO_IP_ST3.1:
    ; nz, get it
    RECEIVE_DATA
    ld  e,a
TCPIP_GET_IPINFO_IP_ST4:
    CHECK_DATA
    jr  nz,TCPIP_GET_IPINFO_IP_ST4.1
    call    TCPIP_GENERIC_CHECK_TIME_OUT
    jr  TCPIP_GET_IPINFO_IP_ST4
TCPIP_GET_IPINFO_IP_ST4.1:
    ; nz, get it
    RECEIVE_DATA
    ld  d,a
    ; done
    xor a
    ret

;=========================
;===  TCPIP_NET_STATE  ===
;=========================
;Get network state.
;
;Input:  A = 3
;Output: A = Error code
;        B = Current network state:
;            0: Closed
;            1: Opening
;            2: Open
;            3: Closing
;            255: Unknown
TCPIP_NET_STATE:
    SEND_DATA                       ; Send the command
    xor a
    SEND_DATA                       ; Send the command size msb
    SEND_DATA                       ; Send the command size lsb

    ; Now wait up to 720 ticks to get response
    ld  hl,720
    call    SETCOUNTER
TCPIP_NET_STATE_ST1:
    CHECK_DATA
    jr  nz,TCPIP_NET_STATE_ST1.1
    call    TCPIP_GENERIC_CHECK_TIME_OUT
    jr  TCPIP_NET_STATE_ST1
TCPIP_NET_STATE_ST1.1:
    ; nz, check the data
    RECEIVE_DATA
    cp  3                           ; Is response of our command?
    jr  nz,TCPIP_NET_STATE_ST1
    ; now get return code, if return code other than 0, it is finished
TCPIP_NET_STATE_RC:
    CHECK_DATA
    jr  nz,TCPIP_NET_STATE_RC.1
    call    TCPIP_GENERIC_CHECK_TIME_OUT
    jr  TCPIP_NET_STATE_RC
TCPIP_NET_STATE_RC.1:
    ; nz, get it
    RECEIVE_DATA
    or  a                           ; 0?
    ret nz                          ; if not, done

    ; next two bytes are return code and size bytes, don't care, it is 1
    ld  b,2
TCPIP_NET_STATE_ST2:
    CHECK_DATA
    jr  nz,TCPIP_NET_STATE_ST2.1
    call    TCPIP_GENERIC_CHECK_TIME_OUT
    jr  TCPIP_NET_STATE_ST2
TCPIP_NET_STATE_ST2.1:
    ; nz, discard
    RECEIVE_DATA
    dec b
    jr  nz,TCPIP_NET_STATE_ST2

    ; now just get the 1 byte (NET STATE) IP and place it in B
TCPIP_NET_STATE_NS_ST1:
    CHECK_DATA
    jr  nz,TCPIP_NET_STATE_NS_ST1.1
    call    TCPIP_GENERIC_CHECK_TIME_OUT
    jr  TCPIP_NET_STATE_NS_ST1
TCPIP_NET_STATE_NS_ST1.1:
    ; nz, get it
    RECEIVE_DATA
    ld  b,a
    ; done
    xor a
    ret

;=====================
;===  TCPIP_DNS_Q  ===
;=====================
;Start a host name resolution query.
;
;Input:  A  = 6
;        HL = Address of the host name to be resolved, zero terminated
;        B  = Flags, when set to 1 they instruct the resolver to:
;             bit 0: Only abort the query currently in progress, if there is any
;                    (other flags and registers are then ignored)
;             bit 1: Assume that the passed name is an IP address,
;                    and return an error if this is not true
;             bit 2: If there is a query in progress already,
;                    do NOT abort it and return an error instead
;Output:  A = Error code
;         B = 0 if a query to a DNS server is in progress
;             1 if the name represented an IP address
;             2 if the name could be resolved locally
;         L.H.E.D = Resolved IP address
;                   (only if no error occurred and B=1 or 2 is returned)
;RAM Buffer to store names to be resolved (and used also to translate IPs from ASCII to 32bits number)
;Will store the result of the last DNS query
TCPIP_DNS_Q:
    push    hl                      ; Save HL
    xor a
    ld  e,a
    ld  d,a                         ; Zero DE
TCPIP_DNS_Q_SIZE_LOOP:
    ld  a,(hl)                      ; so let's check the size of dns data
    or  a                           ; it is zero terminated
    jr  z,TCPIP_DNS_Q_SEND          ; if zero, end of string
    inc de                          ; ok, not zero, one more char
    inc hl                          ; next
    jp  TCPIP_DNS_Q_SIZE_LOOP       ; jp is a tad bit faster and we are not worried about code size
TCPIP_DNS_Q_SEND:
    ; Here we send the query and wait the result
    inc de                          ; add 1, we will send flag first
    ld  a,206                       ; DNS_Q_NEW
    SEND_DATA                       ; Send the command
    ld  a,d
    SEND_DATA                       ; Send the command size msb
    ld  a,e
    SEND_DATA                       ; Send the command size lsb
    ld  a,b
    SEND_DATA                       ; Send the flag byte

    if USE_MEM_IO = 0
    ; now otir of DNS/DNS BUFFER DATA SIZE
    ld  c,OUT_TX_PORT               ; our data TX port
    endif
    pop hl                          ; string to try to resolve
    dec de                          ; we are sending just data addressed by HL, so revert count
    ld  a,d
    or  e                           ; if de zero, no string, wrong parameters, but let the ESP answer
    jp  z,TCPIP_DNS_Q_WAIT_RSP
    xor a
    ; Fast 16 bit variable size loop by GRAUW
    ld  b,e
    dec de
    inc d
TCPIP_DNS_Q_SENDLP:
    ; send it
    if USE_MEM_IO = 0
    outi
    jp  nz,TCPIP_DNS_Q_SENDLP
    else
    ld  a,(hl)
    ld  (MEM_OUT_TX_PORT),a
    inc hl
    djnz TCPIP_DNS_Q_SENDLP
    endif
    dec d
    jp  nz,TCPIP_DNS_Q_SENDLP
TCPIP_DNS_Q_WAIT_RSP:
    ; Now wait up to 900 ticks (15s@60Hz) to get response
    ld  hl,900
    call    SETCOUNTER
TCPIP_DNSQ_SEND_ST1:
    CHECK_DATA
    jr  nz,TCPIP_DNSQ_SEND_ST1.1
    call    TCPIP_GENERIC_CHECK_TIME_OUT
    jr  TCPIP_DNSQ_SEND_ST1
TCPIP_DNSQ_SEND_ST1.1:
    ; nz, check the data
    RECEIVE_DATA
    cp  206                         ; Is response of our command?
    jr  nz,TCPIP_DNSQ_SEND_ST1
    ; now get return code, if return code other than 0, it is finished
TCPIP_DNSQ_SEND_RC:
    CHECK_DATA
    jr  nz,TCPIP_DNSQ_SEND_RC.1
    call    TCPIP_GENERIC_CHECK_TIME_OUT
    jr  TCPIP_DNSQ_SEND_RC
TCPIP_DNSQ_SEND_RC.1:
    ; nz, discard
    RECEIVE_DATA
    or  a                           ; 0?
    ld  b,0                         ; say in progress as there is no failure status
    ret nz                          ; if not, done, ERROR won't return data

    ; next two bytes are return code and size bytes, don't care, it is 4, resolved IP
    ld  b,2
TCPIP_DNSQ_SEND_RC_ST2:
    CHECK_DATA
    jr  nz,TCPIP_DNSQ_SEND_RC_ST2.1
    call    TCPIP_GENERIC_CHECK_TIME_OUT
    jr  TCPIP_DNSQ_SEND_RC_ST2
TCPIP_DNSQ_SEND_RC_ST2.1:
    ; nz, discard
    RECEIVE_DATA
    dec b
    jr  nz,TCPIP_DNSQ_SEND_RC_ST2

    ; now just get the 4 bytes IP and place it in L H E D
TCPIP_DNSQ_IP_ST1:
    CHECK_DATA
    jr  nz,TCPIP_DNSQ_IP_ST1.1
    call    TCPIP_GENERIC_CHECK_TIME_OUT
    jr  TCPIP_DNSQ_IP_ST1
TCPIP_DNSQ_IP_ST1.1:
    ; nz, get it
    RECEIVE_DATA
    ld  l,a
TCPIP_DNSQ_IP_ST2:
    CHECK_DATA
    jr  nz,TCPIP_DNSQ_IP_ST2.1
    call    TCPIP_GENERIC_CHECK_TIME_OUT
    jr  TCPIP_DNSQ_IP_ST2
TCPIP_DNSQ_IP_ST2.1:
    ; nz, get it
    RECEIVE_DATA
    ld  h,a
TCPIP_DNSQ_IP_ST3:
    CHECK_DATA
    jr  nz,TCPIP_DNSQ_IP_ST3.1
    call    TCPIP_GENERIC_CHECK_TIME_OUT
    jr  TCPIP_DNSQ_IP_ST3
TCPIP_DNSQ_IP_ST3.1:
    ; nz, get it
    RECEIVE_DATA
    ld  e,a
TCPIP_DNSQ_IP_ST4:
    CHECK_DATA
    jr  nz,TCPIP_DNSQ_IP_ST4.1
    call    TCPIP_GENERIC_CHECK_TIME_OUT
    jr  TCPIP_DNSQ_IP_ST4
TCPIP_DNSQ_IP_ST4.1:
    ; nz, get it
    RECEIVE_DATA
    ld  d,a
    ; done
    ld  a,1
    call    SETDNSREADY             ; DNS done
    call    SETDNSRESULT            ; DNS RESULT
    ld  b,2
    xor a
    ret

;=====================
;===  TCPIP_DNS_S  ===
;=====================
;Obtains the host name resolution process state and result.
;
;Input:  A = 7
;        B = Flags, when set to 1 they instruct the resolver to:
;            bit 0: Clear any existing result or error condition after the execution
;                   (except if there is a query in progress)
;Output: A = Error code
;        B = DNS error code (when error is ERR_DNS)
;        B = Current query status (when error is ERR_OK):
;            0: There is no query in progress, nor any result nor error code available
;            1: There is a query in progress
;            2: Query is complete
;        C = Current query sub status (when error is ERR_OK and B=1):
;            0: Unknown
;            1: Querying the primary DNS server
;            2: Querying the secondary DNS server
;            3: Querying another DNS server
;        C = Resolution process type (when error is ERR_OK and B=2):
;            0: The name was obtained by querying a DNS server
;            1: The name was a direct representation of an IP address
;            2: The name was resolved locally
;       L.H.E.D = Resolved IP address (when error is ERR_OK and B=2)
TCPIP_DNS_S:
    ;--- Is there a result?
    call    GETDNSREADY             ; DNS done?
    or  a
    jr  z,TCPIP_DNS_S_NORESULT      ; No DNS result
    ;--- Ok, we have a result, is it success?
    dec a
    jr  z,TCPIP_DNS_S_HASRESULT     ; If it is 1, it was not an error
    ;--- Shoot, there is an error...
    ;--- And sure thing, ESP do not tell us details, it is always failure :-P
    bit 0,b                         ;--- clear error after this?
    jr  z,TCP_IP_DNS_S_NOCLR
    ;--- Clear
    ld b,0                          ;--- Like I've said, no details
    xor a
    call    SETDNSREADY             ; DNS not done
    ld  a,ERR_DNS;
    ret
TCP_IP_DNS_S_NOCLR:
    ;--- Don't clear
    ld  a,ERR_DNS
    ld  b,0                         ;--- Like I've said, no details
    ret
    ;--- There is a result available...
TCPIP_DNS_S_HASRESULT:
    ;--- Copy the result
    call    GETDNSRESULT
    xor a
    bit 0,b                         ;--- clear result after this?
    jr  z,TCP_IP_DNS_S_RES_NOCLR    ;--- no, just return
    ;--- Yes, clear
    call    SETDNSREADY             ; DNS not done
TCP_IP_DNS_S_RES_NOCLR:
    ld  b,2
    ret

TCPIP_DNS_S_NORESULT:
    xor a                           ;--- OK no query in progress, no result, means nothing in progress
    ld  b,0                         ;--- No query in progress
    ret

;========================
;===  TCPIP_UDP_OPEN  ===
;========================
;Open an UDP connection.
;
;Input:  A  = 8
;        HL = Local port number (#FFFF=random)
;        B  = Intended connection lifetime:
;             0: Transient
;             1: Resident
;Output: A = Error code
;        B = Connection number
TCPIP_UDP_OPEN:
    SEND_DATA                       ; Send the command
    xor a
    SEND_DATA                       ; Send the command size msb
    ld  a,3
    SEND_DATA                       ; Send the command size lsb
    ld  a,l
    SEND_DATA                       ; Send the port LSB
    ld  a,h
    SEND_DATA                       ; Send the port MSB
    ld  a,b
    SEND_DATA                       ; Send the connection transient/resident

    ; Now wait up to 180 ticks to get response
    ld  hl,180
    call    SETCOUNTER
TCPIP_UDP_OPEN_ST1:
    CHECK_DATA
    jr  nz,TCPIP_UDP_OPEN_ST1.1
    call    TCPIP_GENERIC_CHECK_TIME_OUT
    jr  TCPIP_UDP_OPEN_ST1
TCPIP_UDP_OPEN_ST1.1:
    ; nz, check the data
    RECEIVE_DATA
    cp  8                           ; Is response of our command?
    jr  nz,TCPIP_UDP_OPEN_ST1
    ; now get return code, if return code other than 0, it is finished
TCPIP_UDP_OPEN_RC:
    CHECK_DATA
    jr  nz,TCPIP_UDP_OPEN_RC.1
    call    TCPIP_GENERIC_CHECK_TIME_OUT
    jr  TCPIP_UDP_OPEN_RC
TCPIP_UDP_OPEN_RC.1:
    ; nz, discard
    RECEIVE_DATA
    or  a                           ; 0?
    ret nz                          ; if not, done

    ; next two bytes are return code and size bytes, don't care, it is 1, conn #
    ld  b,2
TCPIP_UDP_OPEN_ST2:
    CHECK_DATA
    jr  nz,TCPIP_UDP_OPEN_ST2.1
    call    TCPIP_GENERIC_CHECK_TIME_OUT
    jr  TCPIP_UDP_OPEN_ST2
TCPIP_UDP_OPEN_ST2.1:
    ; nz, discard
    RECEIVE_DATA
    dec b
    jr  nz,TCPIP_UDP_OPEN_ST2

    ; now just get the 1 byte, conn#, should go to B
TCPIP_UDP_OPEN_CONN_ST1:
    CHECK_DATA
    jr  nz,TCPIP_UDP_OPEN_CONN_ST1.1
    call    TCPIP_GENERIC_CHECK_TIME_OUT
    jr  TCPIP_UDP_OPEN_CONN_ST1
TCPIP_UDP_OPEN_CONN_ST1.1:
    ; nz, get it
    RECEIVE_DATA
    ld  b,a
    ; done
    xor a
    ret

;=========================
;===  TCPIP_UDP_CLOSE  ===
;=========================
;Close a UDP connection.
;
;Input:  A = 9
;        B = Connection number
;            0 to close all open transient UDP connections
;Output: A = Error code
TCPIP_UDP_CLOSE:
    SEND_DATA                       ; Send the command
    xor a
    SEND_DATA                       ; Send the command size msb
    ld  a,1
    SEND_DATA                       ; Send the command size lsb
    ld  a,b
    SEND_DATA                       ; Send the connection #
    ; Now wait up to 180 ticks to get response
    ld  hl,180
    call    SETCOUNTER
TCPIP_UDP_CLOSE_ST1:
    CHECK_DATA
    jr  nz,TCPIP_UDP_CLOSE_ST1.1
    call    TCPIP_GENERIC_CHECK_TIME_OUT
    jr  TCPIP_UDP_CLOSE_ST1
TCPIP_UDP_CLOSE_ST1.1:
    ; nz, check the data
    RECEIVE_DATA
    cp  9                           ; Is response of our command?
    jr  nz,TCPIP_UDP_CLOSE_ST1
    ; now get return code, if return code other than 0, it is finished
TCPIP_UDP_CLOSE_RC:
    CHECK_DATA
    jr  nz,TCPIP_UDP_CLOSE_RC.1
    call    TCPIP_GENERIC_CHECK_TIME_OUT
    jr  TCPIP_UDP_CLOSE_RC
TCPIP_UDP_CLOSE_RC.1:
    ; nz, discard
    RECEIVE_DATA
    or  a                           ; 0?
    ret nz                          ; if not, done

    ; next two bytes are return code and size bytes, don't care, it is 1, conn #
    ld  b,2
TCPIP_UDP_CLOSE_ST2:
    CHECK_DATA
    jr  nz,TCPIP_UDP_CLOSE_ST2.1
    call    TCPIP_GENERIC_CHECK_TIME_OUT
    jr  TCPIP_UDP_CLOSE_ST2
TCPIP_UDP_CLOSE_ST2.1:
    ; nz, discard
    RECEIVE_DATA
    dec b
    jr  nz,TCPIP_UDP_CLOSE_ST2

    ; done, no return data other than return code
    xor a
    ret

;=========================
;===  TCPIP_UDP_STATE  ===
;=========================
;Get the state of a UDP connection.
;
;Input:  A = 10
;        B = Connection number
;Output: A  = Error code
;        HL = Local port number
;        B  = Number of pending incoming datagrams
;        DE = Size of oldest pending incoming datagram (data part only)
TCPIP_UDP_STATE:
    SEND_DATA                       ; Send the command
    xor a
    SEND_DATA                       ; Send the command size msb
    inc a
    SEND_DATA                       ; Send the command size lsb
    ld  a,b
    SEND_DATA                       ; Send the parameter

    ; Now wait up to 60 ticks to get response
    ld  hl,60
    call    SETCOUNTER
TCPIP_UDP_STATE_ST1:
    CHECK_DATA
    jr  nz,TCPIP_UDP_STATE_ST1.1
    call    TCPIP_GENERIC_CHECK_TIME_OUT
    jr  TCPIP_UDP_STATE_ST1
TCPIP_UDP_STATE_ST1.1:
    ; nz, check the data
    RECEIVE_DATA
    cp  10                          ; Is response of our command?
    jr  nz,TCPIP_UDP_STATE_ST1
    ; now get return code, if return code other than 0, it is finished
TCPIP_UDP_STATE_RC:
    CHECK_DATA
    jr  nz,TCPIP_UDP_STATE_RC.1
    call    TCPIP_GENERIC_CHECK_TIME_OUT
    jr  TCPIP_UDP_STATE_RC
TCPIP_UDP_STATE_RC.1:
    ; nz, discard
    RECEIVE_DATA
    or  a                           ; 0?
    ret nz                          ; if not, done

    ; next two bytes are return code and size bytes, don't care, it is 5
    ld  b,2
TCPIP_UDP_STATE_ST2:
    CHECK_DATA
    jr  nz,TCPIP_UDP_STATE_ST2.1
    call    TCPIP_GENERIC_CHECK_TIME_OUT
    jr  TCPIP_UDP_STATE_ST2
TCPIP_UDP_STATE_ST2.1:
    ; nz, discard
    RECEIVE_DATA
    dec b
    jr  nz,TCPIP_UDP_STATE_ST2

    ; now just get the 5 bytes (Port LSB then MSB, # of packets, packet size LSB then MSB) and order it in L, H, B, E and D
TCPIP_UDP_STATE_RESP_ST1:
    CHECK_DATA
    jr  nz,TCPIP_UDP_STATE_RESP_ST1.1
    call    TCPIP_GENERIC_CHECK_TIME_OUT
    jr  TCPIP_UDP_STATE_RESP_ST1
TCPIP_UDP_STATE_RESP_ST1.1:
    ; nz, get it
    RECEIVE_DATA
    ld  l,a
TCPIP_UDP_STATE_RESP_ST2:
    CHECK_DATA
    jr  nz,TCPIP_UDP_STATE_RESP_ST2.1
    call    TCPIP_GENERIC_CHECK_TIME_OUT
    jr  TCPIP_UDP_STATE_RESP_ST2
TCPIP_UDP_STATE_RESP_ST2.1:
    ; nz, get it
    RECEIVE_DATA
    ld  h,a
TCPIP_UDP_STATE_RESP_ST3:
    CHECK_DATA
    jr  nz,TCPIP_UDP_STATE_RESP_ST3.1
    call    TCPIP_GENERIC_CHECK_TIME_OUT
    jr  TCPIP_UDP_STATE_RESP_ST3
TCPIP_UDP_STATE_RESP_ST3.1:
    ; nz, get it
    RECEIVE_DATA
    ld  b,a
TCPIP_UDP_STATE_RESP_ST4:
    CHECK_DATA
    jr  nz,TCPIP_UDP_STATE_RESP_ST4.1
    call    TCPIP_GENERIC_CHECK_TIME_OUT
    jr  TCPIP_UDP_STATE_RESP_ST4
TCPIP_UDP_STATE_RESP_ST4.1:
    ; nz, get it
    RECEIVE_DATA
    ld  e,a
TCPIP_UDP_STATE_RESP_ST5:
    CHECK_DATA
    jr  nz,TCPIP_UDP_STATE_RESP_ST5.1
    call    TCPIP_GENERIC_CHECK_TIME_OUT
    jr  TCPIP_UDP_STATE_RESP_ST5
TCPIP_UDP_STATE_RESP_ST5.1:
    ; nz, get it
    RECEIVE_DATA
    ld  d,a
    ; done
    xor a
    ret

;========================
;===  TCPIP_UDP_SEND  ===
;========================
;Send an UDP datagram.
;
;Input:  A = 11
;        B = Connection number
;        HL = Address of datagram data
;        DE = Address of parameters block
;Output: A = Error code
;
;Parameters block:
;
;    +0 (4): Destination IP address
;    +4 (2): Destination port
;    +6 (2): Data length
TCPIP_UDP_SEND:
    push    hl
    push    de
    SEND_DATA                       ; Send the command
    ; prepare new data size, adding our 7 bytes overhead
    ld  ixh,d
    ld  ixl,e
    ld  de,7
    ld  l,(ix+6)
    ld  h,(ix+7)
    add hl,de
    ld  a,h
    SEND_DATA                       ; Send the command size msb
    ld  a,l
    SEND_DATA                       ; Send the command size lsb
    ld  a,b
    SEND_DATA                       ; Send the connection #
    pop de
    pop hl
    ld  a,(de)
    SEND_DATA                       ; Send IP byte 1
    inc de
    ld  a,(de)
    SEND_DATA                       ; Send IP byte 2
    inc de
    ld  a,(de)
    SEND_DATA                       ; Send IP byte 3
    inc de
    ld  a,(de)
    SEND_DATA                       ; Send IP byte 4
    inc de
    ld  a,(de)
    SEND_DATA                       ; Send Port LSB
    inc de
    ld  a,(de)
    SEND_DATA                       ; Send Port MSB
    ; now oti the data starting at hl, size is in next DE position
    inc de
    ld  a,(de)
    ld  b,a                         ; save lsb in b
    inc de
    ld  a,(de)                      ; msb
    ld  d,a                         ; put in D, there is no ld d,(de)
    ld  e,b                         ; lsb
    ; Grauw Optimized 16 bit loop, handy for us, mostly since we can use outi :-D
    ;ld b,e                         ; Number of loops originaly in DE, not needed, b already has e
    dec de
    inc d
    if USE_MEM_IO = 0
    ld  c,OUT_TX_PORT
TCPIP_UDP_SEND_R:
    otir                            ; Send until B is 0
    else
TCPIP_UDP_SEND_R:
    ld  a,(hl)
    ld  (MEM_OUT_TX_PORT),a
    inc hl
    djnz TCPIP_UDP_SEND_R
    endif
    dec d                           ; decrement secondary counter
    jr  nz,TCPIP_UDP_SEND_R         ; If still have another round, do it
    ; Now wait up to 600 ticks to get response
    ld  hl,600
    call    SETCOUNTER
TCPIP_UDP_SEND_ST1:
    CHECK_DATA
    jr  nz,TCPIP_UDP_SEND_ST1.1
    call    TCPIP_GENERIC_CHECK_TIME_OUT
    jr  TCPIP_UDP_SEND_ST1
TCPIP_UDP_SEND_ST1.1:
    ; nz, check the data
    RECEIVE_DATA
    cp  11                          ; Is response of our command?
    jr  nz,TCPIP_UDP_SEND_ST1
    ; now get return code, if return code other than 0, it is finished
TCPIP_UDP_SEND_RC:
    CHECK_DATA
    jr  nz,TCPIP_UDP_SEND_RC.1
    call    TCPIP_GENERIC_CHECK_TIME_OUT
    jr  TCPIP_UDP_SEND_RC
TCPIP_UDP_SEND_RC.1:
    ; nz, discard
    RECEIVE_DATA
    or  a                           ; 0?
    ret nz                          ; if not, done

    ; next two bytes are return code and size bytes, don't care, it is 0
    ld  b,2
TCPIP_UDP_SEND_ST2:
    CHECK_DATA
    jr  nz,TCPIP_UDP_SEND_ST2.1
    call    TCPIP_GENERIC_CHECK_TIME_OUT
    jr  TCPIP_UDP_SEND_ST2
TCPIP_UDP_SEND_ST2.1:
    ; nz, discard
    RECEIVE_DATA
    dec b
    jr  nz,TCPIP_UDP_SEND_ST2

    ; done, no return data other than return code
    xor a
    ret

;=======================
;===  TCPIP_UDP_RCV  ===
;=======================
;Retrieve an incoming UDP datagram.
;
;Input:  A = 12
;        B = Connection number
;        HL = Address for datagram data
;        DE = Maximum data size to retrieve
;Output: A = Error code
;        L.H.E.D = Source IP address
;        IX = Source port
;        BC = Actual received data size

; Customized TIME OUT routine: If time out receiving data, retry as received data
; won't be re-sent as host is unaware of this
TCPIP_UDP_RCV_CHECK_TIME_OUT:
    ; Save registers other than AF
    push bc
    push de
    push hl
    call    GETCOUNTER
    ld  a,l
    or  h
    ; Restore registers, we are returning
    pop hl
    pop de
    pop bc
    ret nz
    ; Ok, timeout...
    pop af                          ; Get return address of who called this out of the stack, we will return from the function or re-start
TCPIP_TCP_UDP_RETRY_QRCV:
    call    GETBYTE
    or  a
    jr  z,TCPIP_UDP_RCV_CHECK_TIME_OUT.NORXRETRY
    ; Ok, so let's ask ESP to re-send the data and retry receiving it
    dec a
    call    SETBYTE                 ; we are retrying it
    ld  a,'r'                       ; retry transmission command
    SEND_DATA
    jp  TCPIP_UDP_RCV.RXRETRY       ; and retry it
TCPIP_UDP_RCV_CHECK_TIME_OUT.NORXRETRY:
    ld  a,ERR_INV_OPER
    ret                             ; and return the function itself
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
