joskwanten/msx-picoverse/2040/software/opl4test/opl4test.c

#include "pico/stdlib.h"
#include "hardware/pio.h"
#include "hardware/dma.h"
#include "hardware/clocks.h"
#include "hardware/pwm.h"

// Define MSX cartridge interface pins (adjust based on your wiring)
#define ADDR_BASE 0
#define DATA_BASE 8
#define CONTROL_RD 16
#define CONTROL_WR 17
#define CONTROL_CS 18

// YMF278B emulation parameters
#define MAX_VOICES 24
#define SAMPLE_RATE 44100
#define SAMPLE_MEM_SIZE (192 * 1024)

typedef struct {
    uint32_t start_addr;
    uint32_t position;
    uint32_t step;
    uint16_t volume;
    uint8_t active;
    uint8_t loop;
} Voice;

typedef struct {
    Voice voices[MAX_VOICES];
    uint8_t sample_mem[SAMPLE_MEM_SIZE];
    uint8_t registers[256];
    uint8_t current_reg;
    uint8_t status;
} YMF278B;

YMF278B opl4;
uint32_t pwm_wrap;

void init_gpio() {
    // Configure address bus as inputs
    for(int i = 0; i < 16; i++)
        gpio_init(ADDR_BASE + i);
    
    // Configure data bus as bidirectional
    for(int i = 0; i < 8; i++) {
        gpio_init(DATA_BASE + i);
        gpio_set_dir(DATA_BASE + i, GPIO_IN);
    }
    
    // Configure control pins
    gpio_init(CONTROL_RD);
    gpio_init(CONTROL_WR);
    gpio_init(CONTROL_CS);
    gpio_set_dir(CONTROL_RD, GPIO_IN);
    gpio_set_dir(CONTROL_WR, GPIO_IN);
    gpio_set_dir(CONTROL_CS, GPIO_IN);
}

void ymf278b_write(uint8_t reg, uint8_t value) {
    opl4.registers[reg] = value;
    
    // Handle register writes
    switch(reg) {
        case 0x00: // Bank select
            opl4.current_reg = value;
            break;
            
        case 0x01 ... 0x08: // Voice control
            // Handle voice parameters
            break;
            
        case 0x09 ... 0x0F: // FM parameters
            // FM synthesis emulation (optional)
            break;
            
        case 0x10 ... 0x17: // Wave memory control
            // Handle sample memory access
            break;
    }
}

uint8_t ymf278b_read(uint8_t reg) {
    return opl4.registers[reg];
}

void process_voices() {
    // This function should be called periodically to update voice positions
    for(int i = 0; i < MAX_VOICES; i++) {
        if(opl4.voices[i].active) {
            opl4.voices[i].position += opl4.voices[i].step;
            
            // Handle sample looping
            if(opl4.voices[i].position >= opl4.voices[i].start_addr + SAMPLE_MEM_SIZE) {
                if(opl4.voices[i].loop) {
                    opl4.voices[i].position = opl4.voices[i].start_addr;
                } else {
                    opl4.voices[i].active = 0;
                }
            }
        }
    }
}

void pwm_audio_init() {
    gpio_set_function(20, GPIO_FUNC_PWM); // Use GPIO 20 for PWM audio
    uint slice_num = pwm_gpio_to_slice_num(20);
    pwm_config config = pwm_get_default_config();
    
    // Set PWM frequency to match sample rate
    float div = (float)clock_get_hz(clk_sys) / (SAMPLE_RATE * 256);
    pwm_config_set_clkdiv(&config, div);
    pwm_config_set_wrap(&config, 255);
    pwm_init(slice_num, &config, true);
}

void update_audio() {
    int32_t mix = 0;
    
    for(int i = 0; i < MAX_VOICES; i++) {
        if(opl4.voices[i].active) {
            uint32_t pos = opl4.voices[i].position;
            if(pos < SAMPLE_MEM_SIZE) {
                int8_t sample = (int8_t)opl4.sample_mem[pos] - 0x80;
                mix += sample * (opl4.voices[i].volume / 256.0);
            }
        }
    }
    
    // Clamp and output mixed sample
    mix = mix > 127 ? 127 : (mix < -128 ? -128 : mix);
    pwm_set_gpio_level(20, (uint8_t)(mix + 128));
}

void cartridge_loop() {
    while(true) {
        // Wait for chip select
        if(!gpio_get(CONTROL_CS)) {
            uint16_t address = 0;
            for(int i = 0; i < 16; i++)
                address |= gpio_get(ADDR_BASE + i) << i;
            
            if(address >= 0x4000 && address <= 0x7FFF) { // Cartridge area
                if(!gpio_get(CONTROL_WR)) { // Write cycle
                    uint8_t data = 0;
                    for(int i = 0; i < 8; i++)
                        data |= gpio_get(DATA_BASE + i) << i;
                    
                    ymf278b_write(address & 0xFF, data);
                }
                else if(!gpio_get(CONTROL_RD)) { // Read cycle
                    uint8_t data = ymf278b_read(address & 0xFF);
                    gpio_set_dir_out_masked(0xFF << DATA_BASE);
                    for(int i = 0; i < 8; i++)
                        gpio_put(DATA_BASE + i, (data >> i) & 1);
                    
                    // Wait for RD to go high
                    while(!gpio_get(CONTROL_RD));
                    gpio_set_dir_in_masked(0xFF << DATA_BASE);
                }
            }
        }
        process_voices();
    }
}

int main() {
    stdio_init_all();
    init_gpio();
    pwm_audio_init();
    
    // Initialize YMF278B emulation
    memset(&opl4, 0, sizeof(YMF278B));
    
    // Load samples into sample_mem (you'll need to implement this)
    // load_samples(opl4.sample_mem);
    
    cartridge_loop();
    return 0;
}
